lazenyuk-dmitry/SterringWheel/assets/80mm-brushless-fan-sunon-kd1208ptb1-2.snapshot.12/80mm brushless fan (SUNON KD1208PTB1)top.JPG

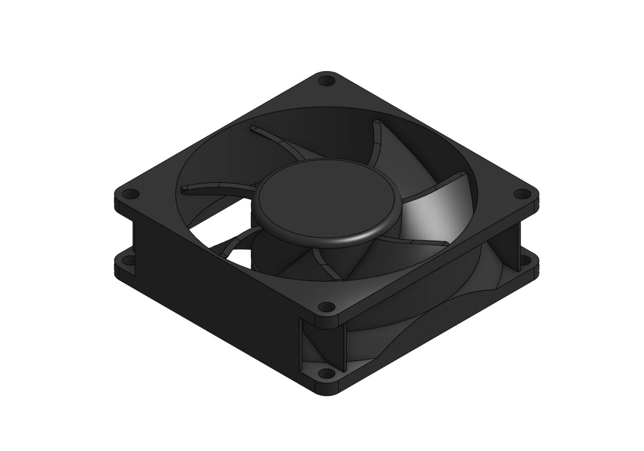
assets/80mm-brushless-fan-sunon-kd1208ptb1-2.snapshot.12/80mm brushless fan (SUNON KD1208PTB1)top.JPG
