lazenyuk-dmitry/SterringWheel/assets/bts7960-43a-high-power-h-bridge-module-1.snapshot.10/BTS7960 43A HIGH POWER H BRIDGE MODULE.JPG

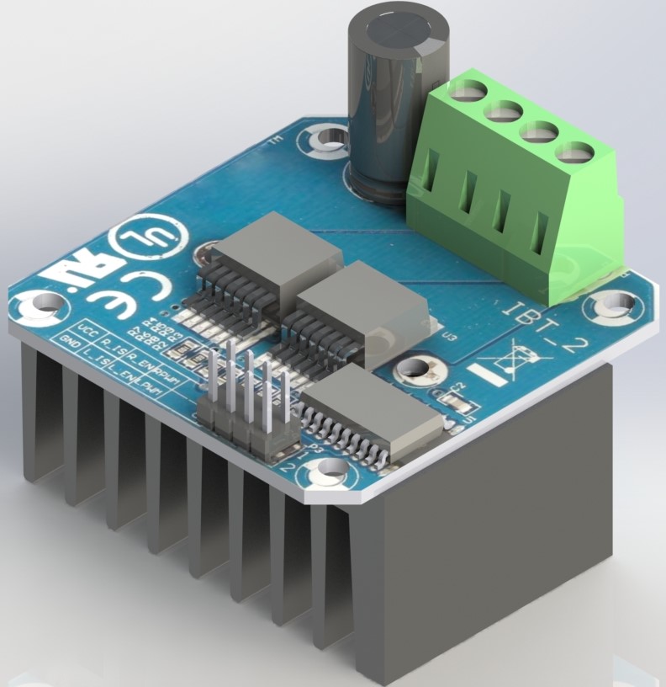
assets/bts7960-43a-high-power-h-bridge-module-1.snapshot.10/BTS7960 43A HIGH POWER H BRIDGE MODULE.JPG
