lazenyuk-dmitry/SterringWheel/assets/connector-5-5x2-5-dc00990-b-1.snapshot.1/Connector_5,5-2,5_DC00990-B_01.png

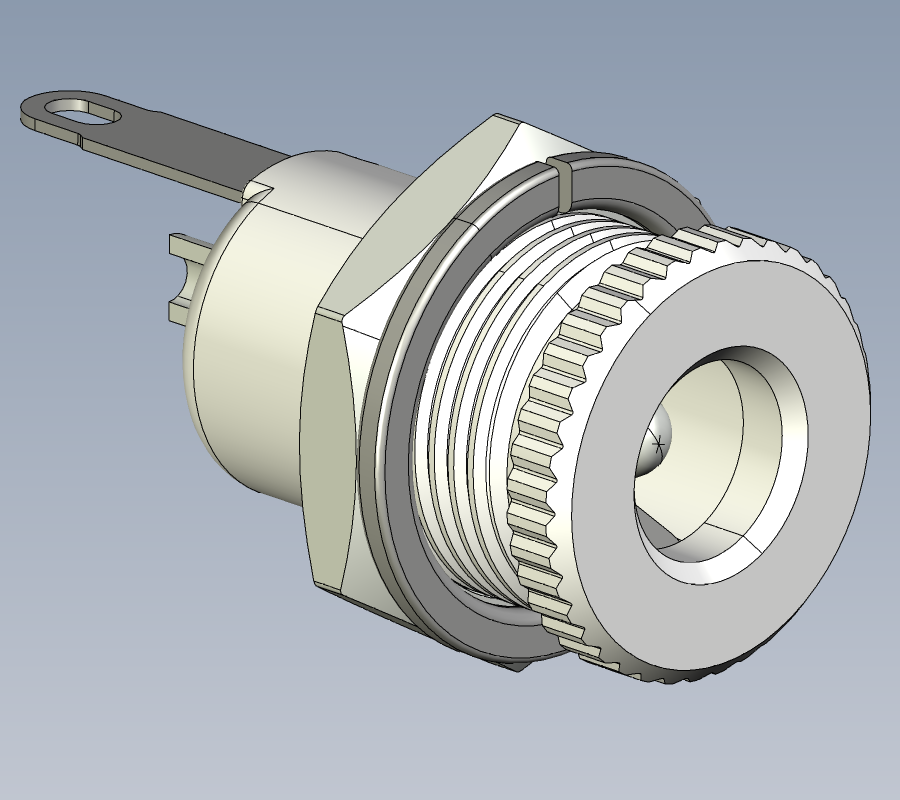
assets/connector-5-5x2-5-dc00990-b-1.snapshot.1/Connector_5,5-2,5_DC00990-B_01.png
