lazenyuk-dmitry/SterringWheel/assets/dc-motor-rs-775-12v-12000-rpm-1.snapshot.1/Capture - 2.PNG

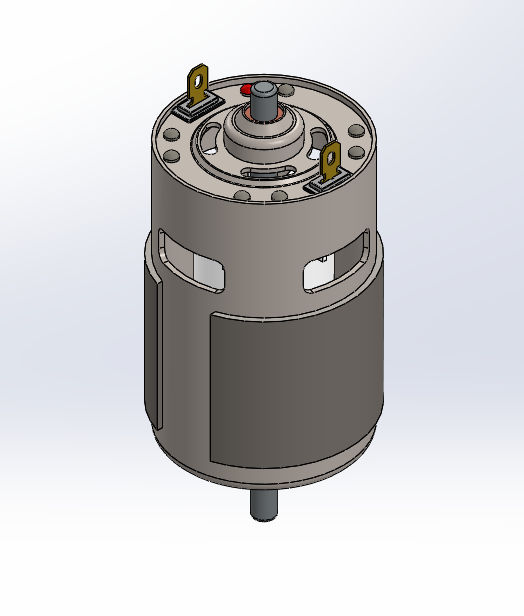
assets/dc-motor-rs-775-12v-12000-rpm-1.snapshot.1/Capture - 2.PNG
