lazenyuk-dmitry/SterringWheel/assets/encoder-36.snapshot.2/untitled.24.jpg

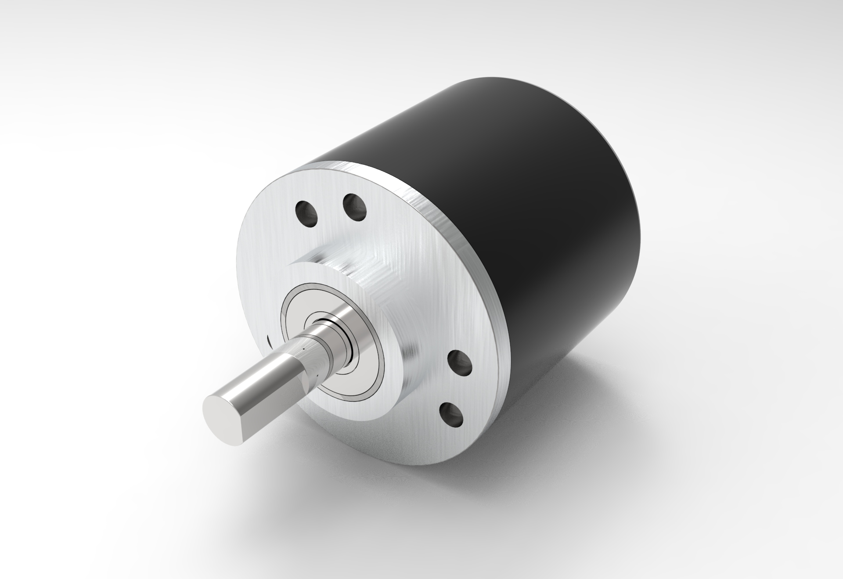
assets/encoder-36.snapshot.2/untitled.24.jpg
