lazenyuk-dmitry/SterringWheel/assets/fanatec-csl-elite-pedals-1.snapshot.8/Rr.png

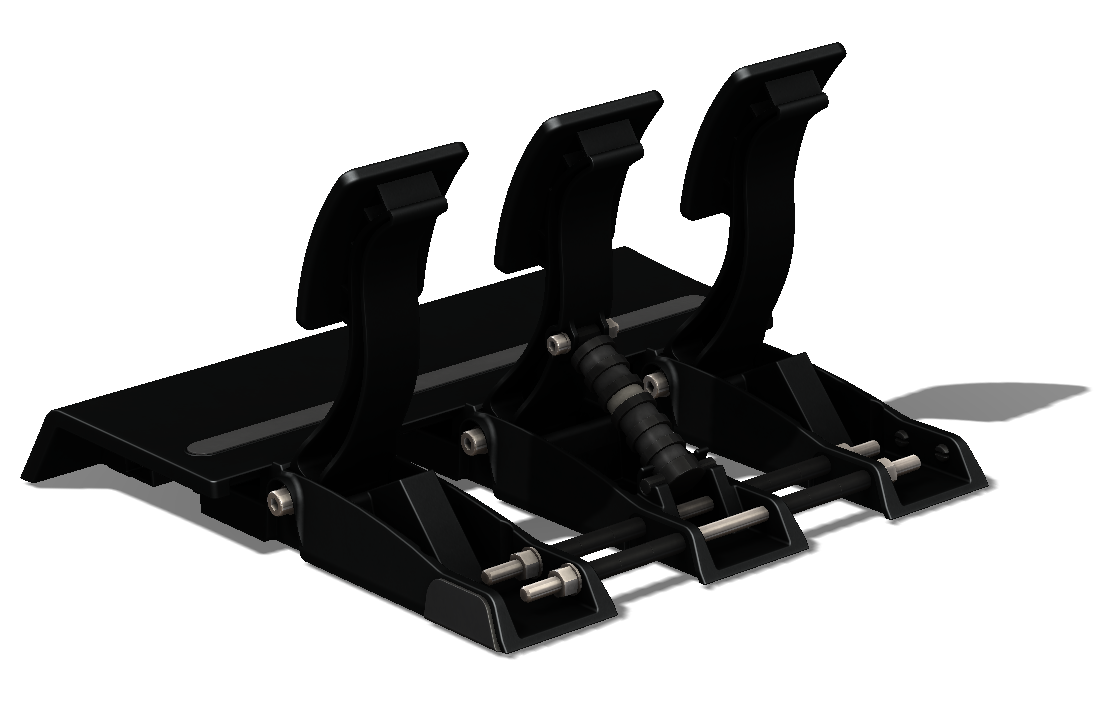
assets/fanatec-csl-elite-pedals-1.snapshot.8/Rr.png
