lazenyuk-dmitry/SterringWheel/assets/fanatec-csp-v2-1.snapshot.5/Renderings/005 gris.png

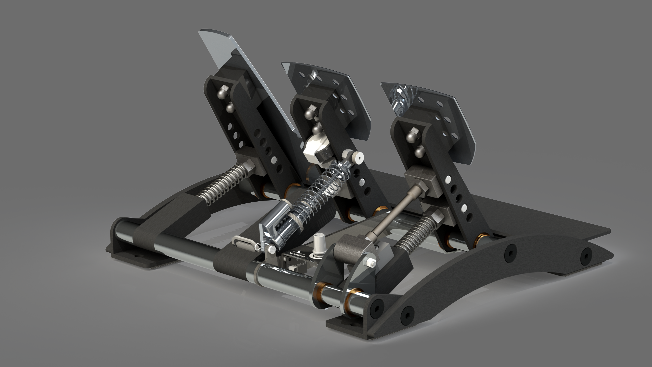
assets/fanatec-csp-v2-1.snapshot.5/Renderings/005 gris.png
