lazenyuk-dmitry/SterringWheel/assets/h-shifter-2.snapshot.1/61ED37vUqIL._SL1019_.jpg

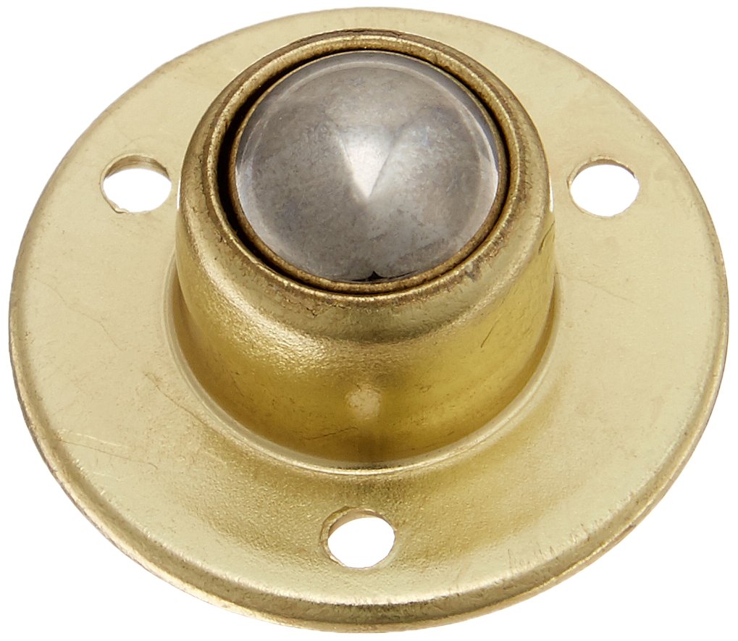
assets/h-shifter-2.snapshot.1/61ED37vUqIL._SL1019_.jpg
