lazenyuk-dmitry/SterringWheel/assets/joy-stick-4.snapshot.1/joy_stick_a2/joy_stick_2a.PNG

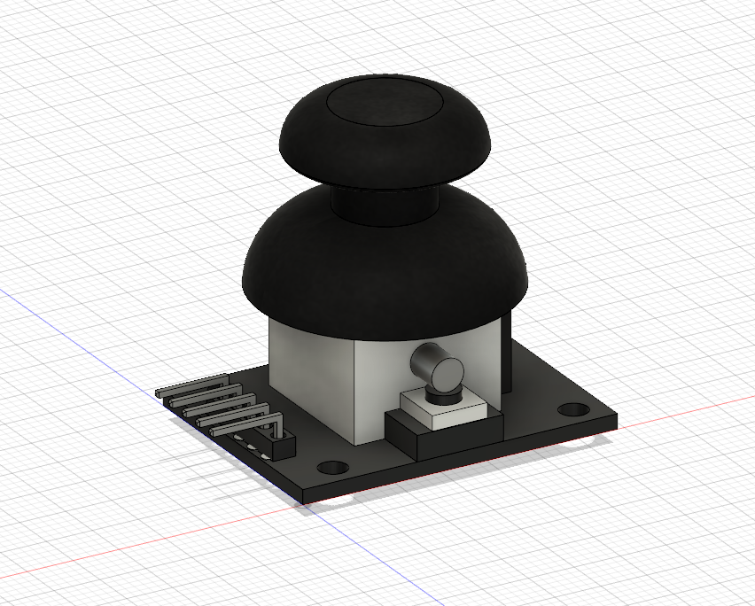
assets/joy-stick-4.snapshot.1/joy_stick_a2/joy_stick_2a.PNG
