lazenyuk-dmitry/SterringWheel/assets/kfl-bearing-or-block-flange-ball-bearing-1.snapshot.10/Bearing KFL series/KFL bearing dimension.JPG

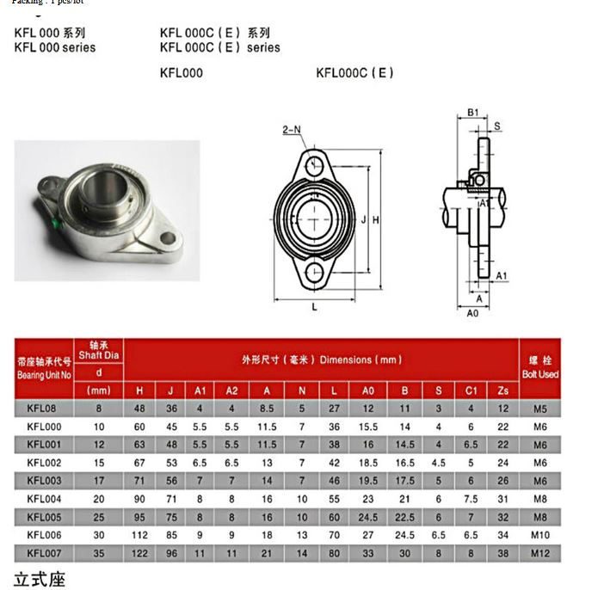
assets/kfl-bearing-or-block-flange-ball-bearing-1.snapshot.10/Bearing KFL series/KFL bearing dimension.JPG
