lazenyuk-dmitry/SterringWheel/assets/kfl-bearing-or-block-flange-ball-bearing-1.snapshot.10/Bearing KFL series/Rendering/KFL006 block flange ball bearing 30 diameter shaft top view.JPG

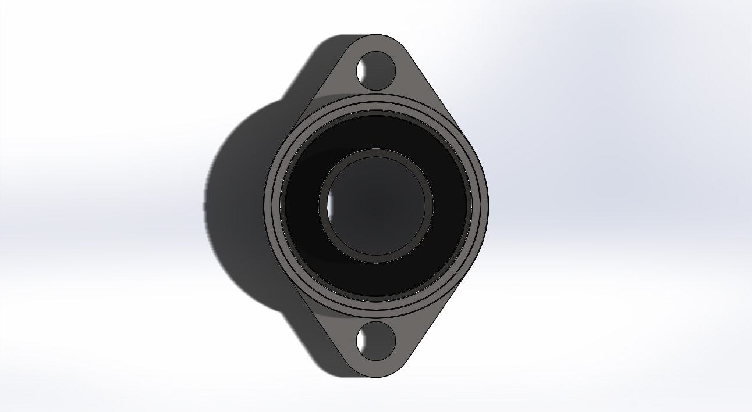
assets/kfl-bearing-or-block-flange-ball-bearing-1.snapshot.10/Bearing KFL series/Rendering/KFL006 block flange ball bearing 30 diameter shaft top view.JPG
