lazenyuk-dmitry/SterringWheel/assets/kfl-bearing-or-block-flange-ball-bearing-1.snapshot.10/Bearing KFL series/Rendering/KFL series with 8 items top.JPG

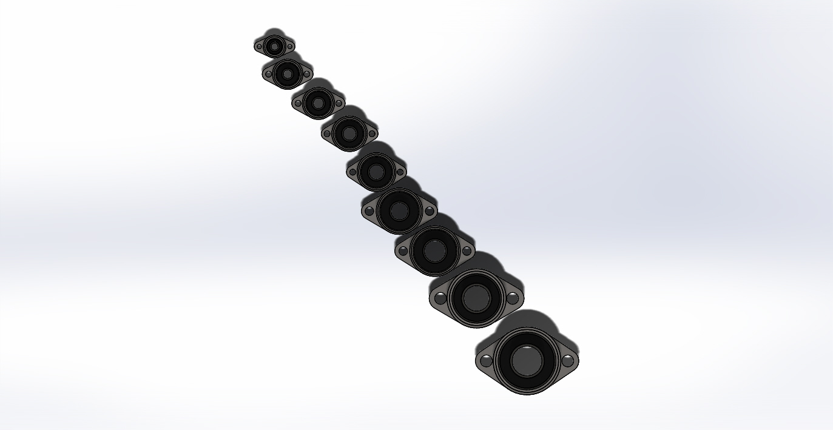
assets/kfl-bearing-or-block-flange-ball-bearing-1.snapshot.10/Bearing KFL series/Rendering/KFL series with 8 items top.JPG
