lazenyuk-dmitry/SterringWheel/assets/lan-rj-45-socket-1.snapshot.3/lan RJ 45 socket.jpg

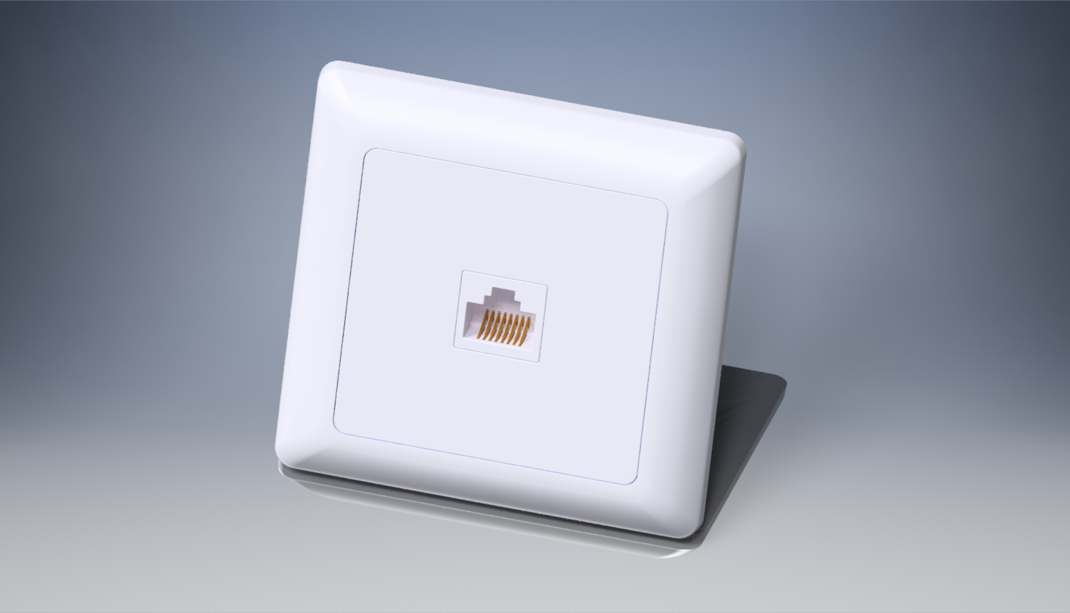
assets/lan-rj-45-socket-1.snapshot.3/lan RJ 45 socket.jpg
