lazenyuk-dmitry/SterringWheel/assets/metal-led-illuminated-latching-16mm-power-push-button-on-off-switch-12v-1.snapshot.2/Metal LED Illuminated Latching 16mm Power Push Button ON-OFF Switch 12V-1.JPG

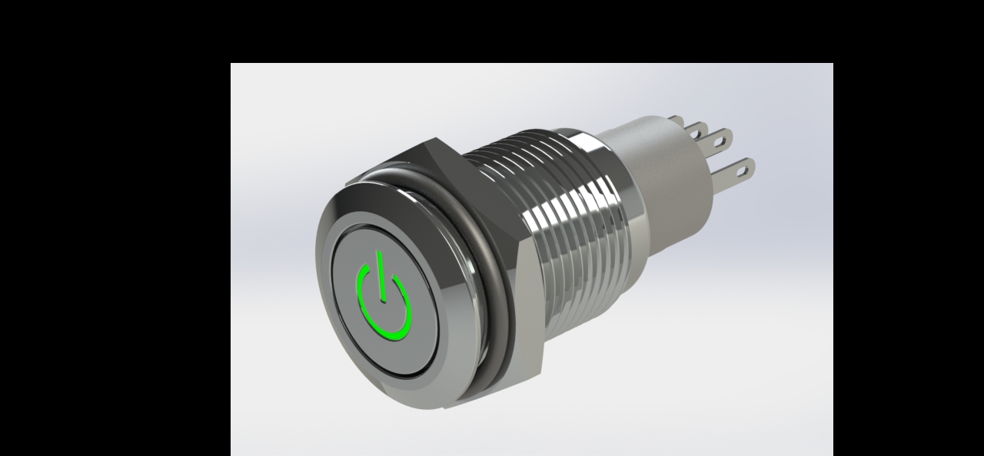
assets/metal-led-illuminated-latching-16mm-power-push-button-on-off-switch-12v-1.snapshot.2/Metal LED Illuminated Latching 16mm Power Push Button ON-OFF Switch 12V-1.JPG
