lazenyuk-dmitry/SterringWheel/assets/micro-switch-with-lever-1.snapshot.3/Micro Switch with Lever.jpg

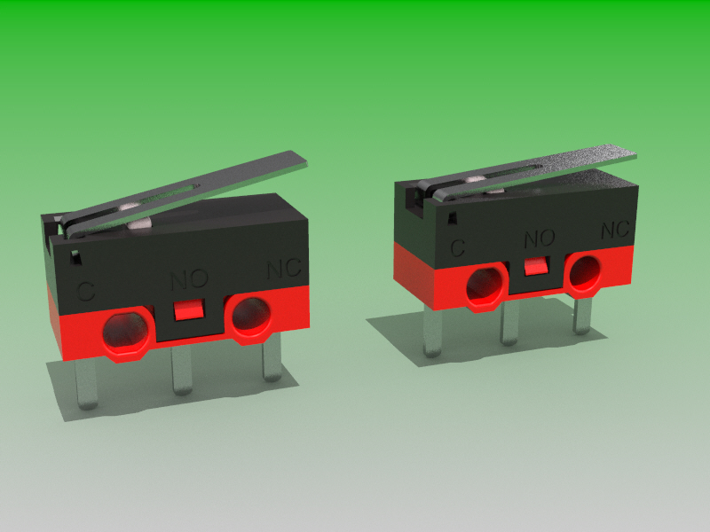
assets/micro-switch-with-lever-1.snapshot.3/Micro Switch with Lever.jpg
