lazenyuk-dmitry/SterringWheel/assets/momentary-push-button-switch-sgi-r13-502-1.snapshot.1/momentary_push_button_sw/momentary_push_button_sw_r13-502p.JPG

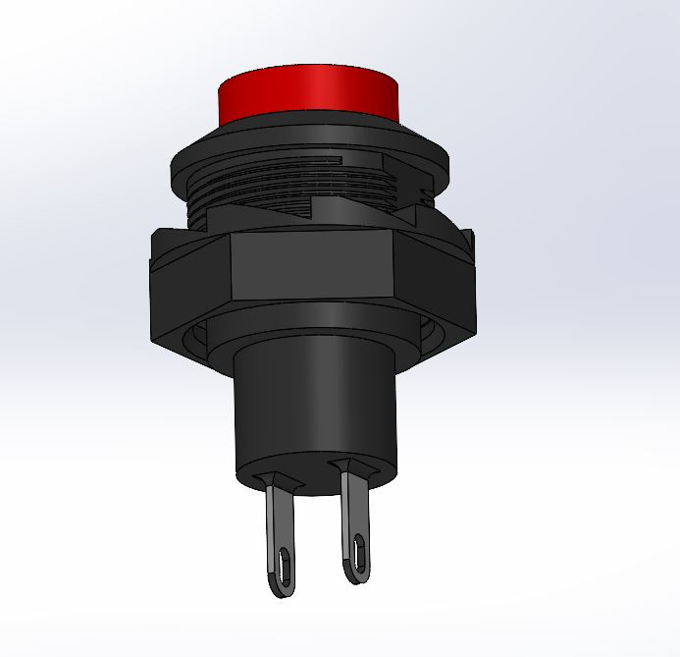
assets/momentary-push-button-switch-sgi-r13-502-1.snapshot.1/momentary_push_button_sw/momentary_push_button_sw_r13-502p.JPG
