lazenyuk-dmitry/SterringWheel/assets/momo-team-300-steering-wheel-1.snapshot.1/momo team 300 steering wheel 2.JPG

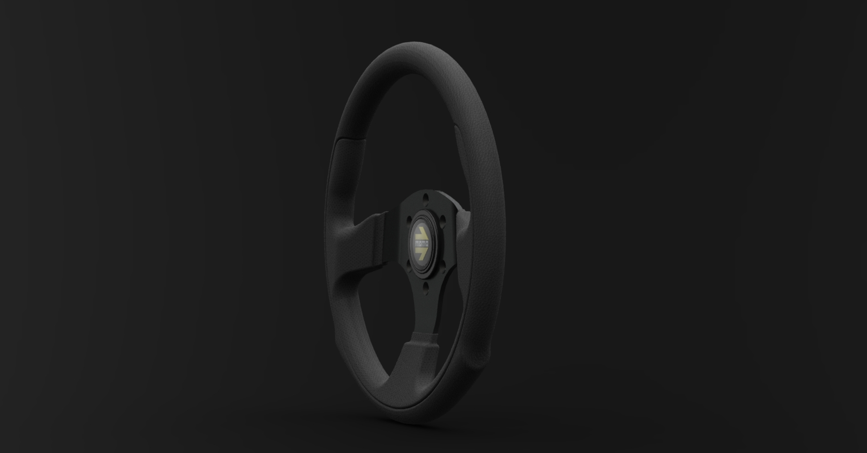
assets/momo-team-300-steering-wheel-1.snapshot.1/momo team 300 steering wheel 2.JPG
