lazenyuk-dmitry/SterringWheel/assets/potentiometer-b10k-3.snapshot.2/potentiometerb10k.jpg

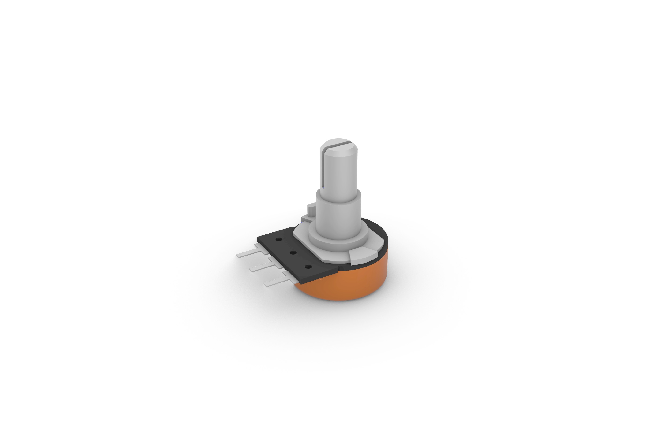
assets/potentiometer-b10k-3.snapshot.2/potentiometerb10k.jpg
