lazenyuk-dmitry/SterringWheel/assets/rocker-switch-arcolectric-r13-112c-aaa-1.snapshot.2/Renderings/Rocker Switch - Arcolectric R13 112C AAA.jpg

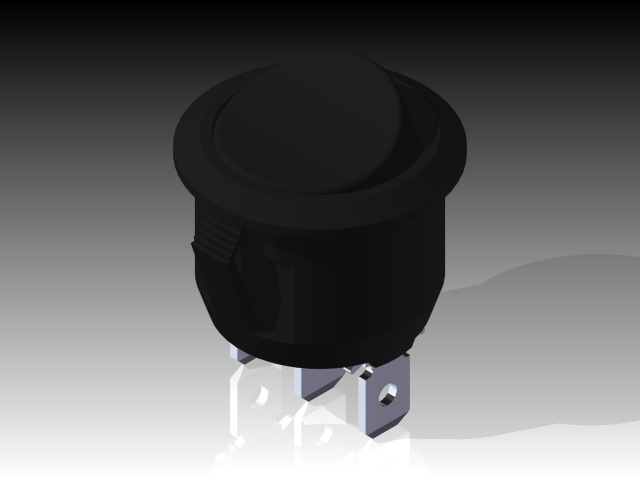
assets/rocker-switch-arcolectric-r13-112c-aaa-1.snapshot.2/Renderings/Rocker Switch - Arcolectric R13 112C AAA.jpg
