lazenyuk-dmitry/SterringWheel/assets/roller-latch/Renderings/pic1.bmp

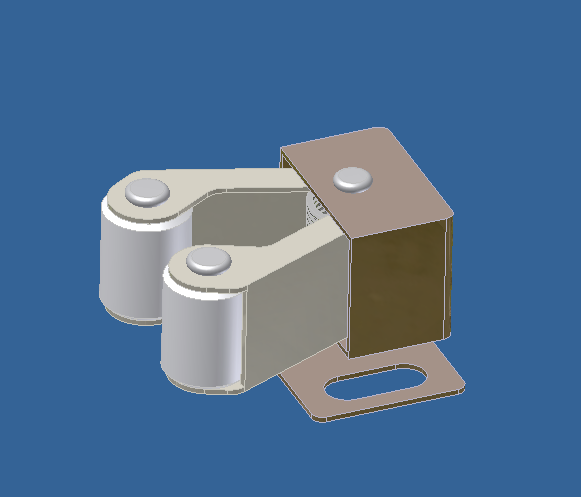
assets/roller-latch/Renderings/pic1.bmp
