lazenyuk-dmitry/SterringWheel/assets/roller-latch/Renderings/pic2.bmp

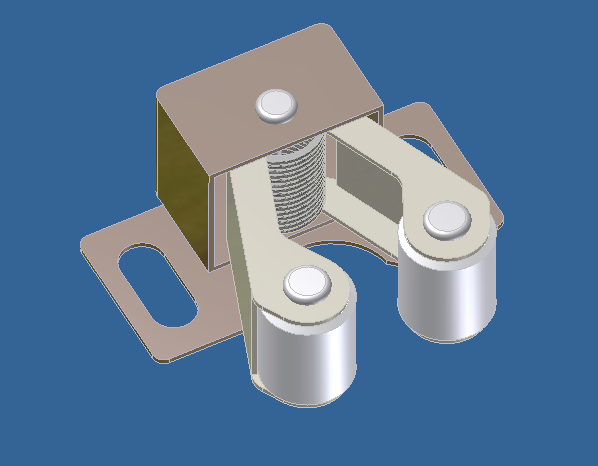
assets/roller-latch/Renderings/pic2.bmp
