lazenyuk-dmitry/SterringWheel/assets/usb-plug-a-1.snapshot.3/USB Plug A.png

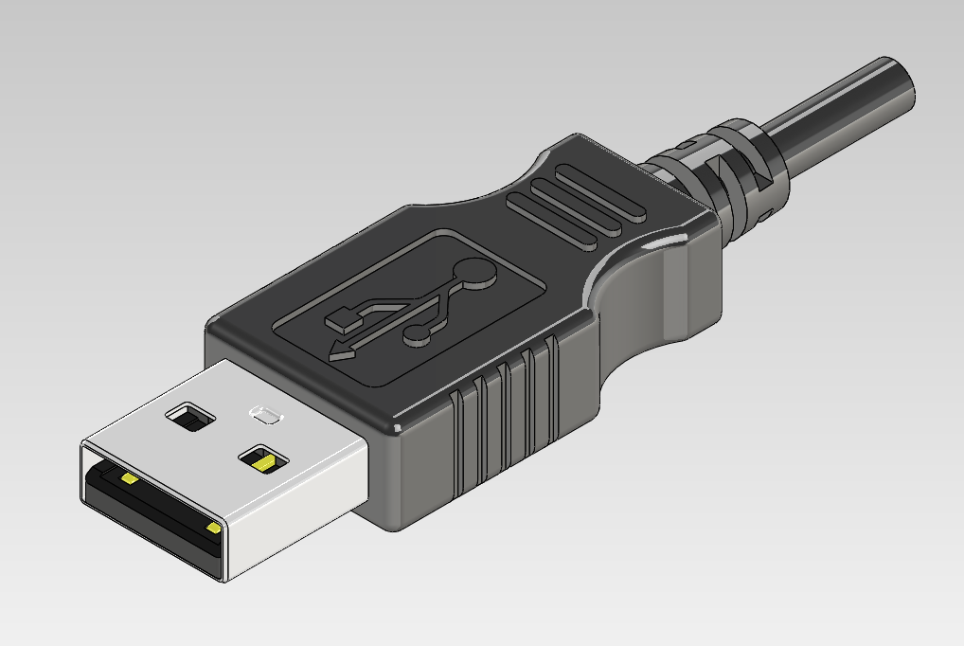
assets/usb-plug-a-1.snapshot.3/USB Plug A.png
