lazenyuk-dmitry/SterringWheel/images/pedals/IMG_20220706_095020.jpg

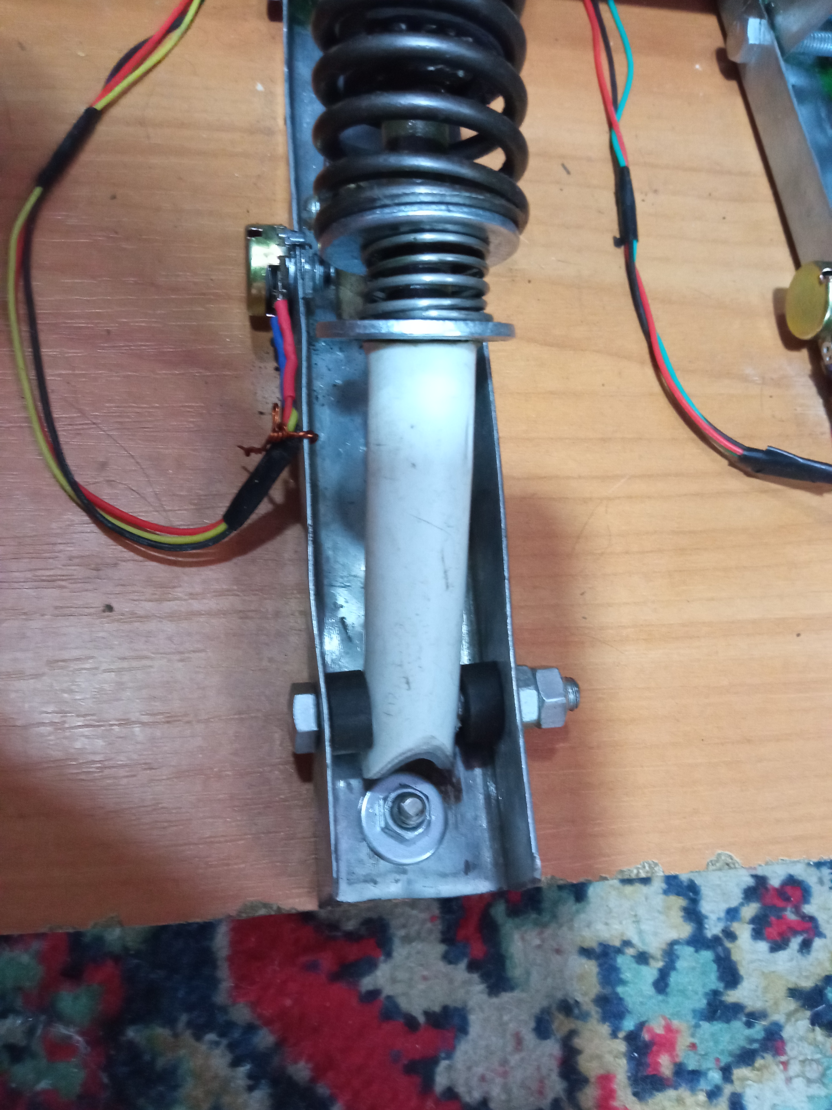
images/pedals/IMG_20220706_095020.jpg
