lazenyuk-dmitry/SterringWheel/images/pedals/IMG_20220706_215036.jpg

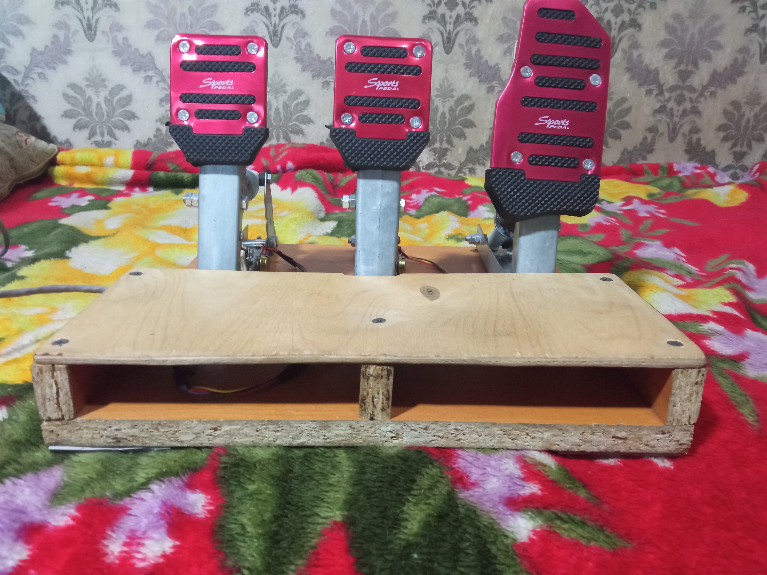
images/pedals/IMG_20220706_215036.jpg
