lazenyuk-dmitry/SterringWheel/images/TopView.png

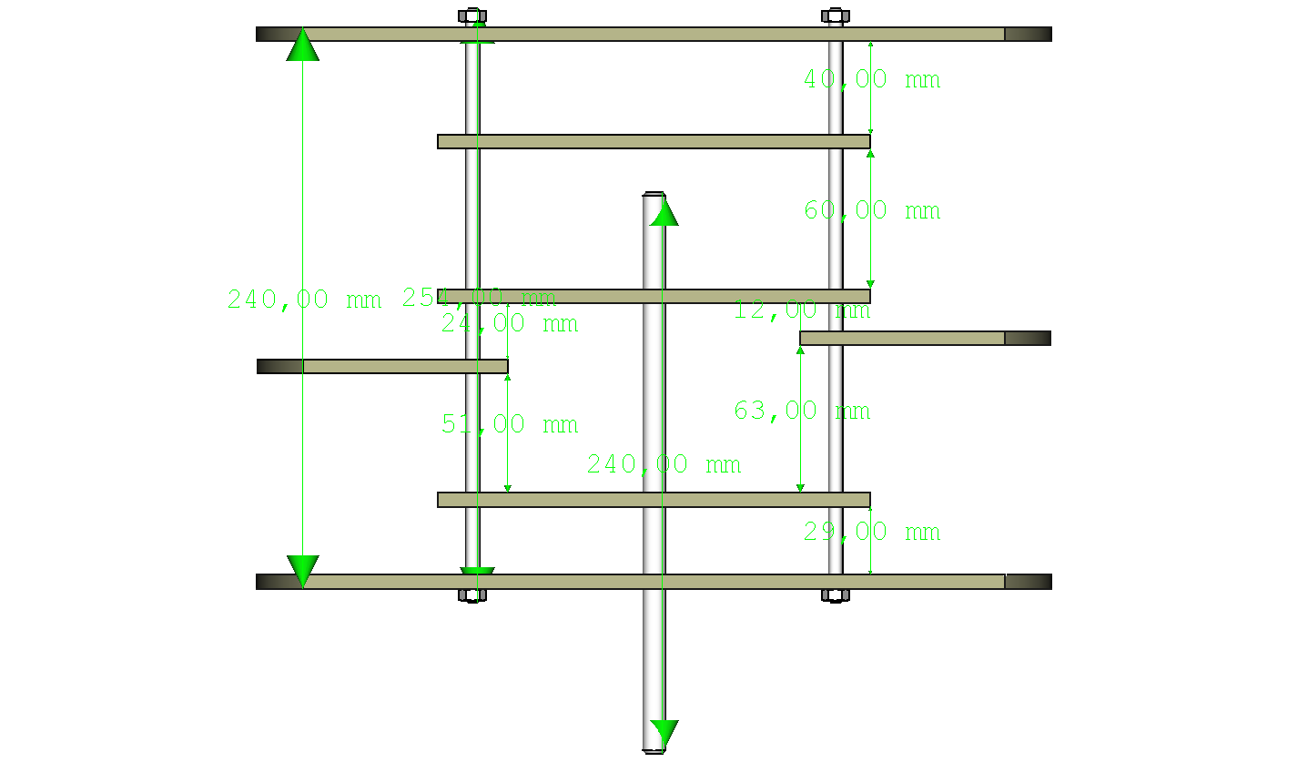
images/TopView.png
