lazenyuk-dmitry/SterringWheel/assets/metal-steering-wheel-1.snapshot.2/vairas.STEP

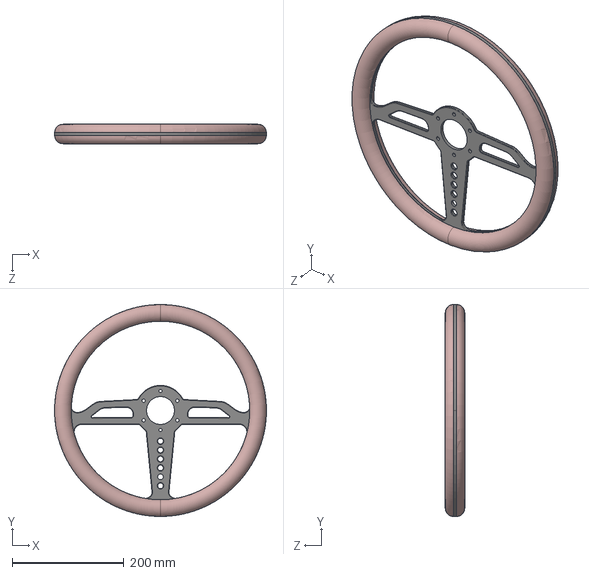
[picture p97: CAD file, 2022-05-22]
assets/metal-steering-wheel-1.snapshot.2/vairas.STEP
380.0 x 380.0 x 35.0 mm
VAIRAS
