lazenyuk-dmitry/SterringWheel/assets/micro-switch-with-lever-1.snapshot.3/Micro Switch with Lever closed.stp

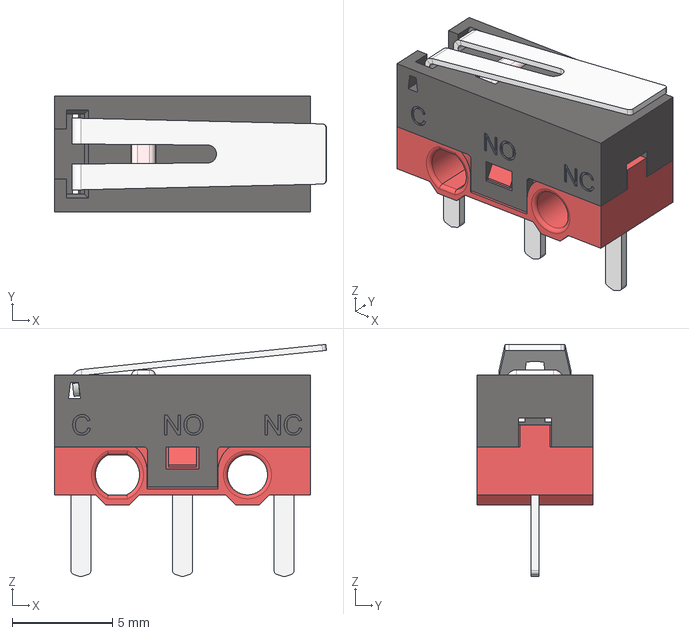
[picture p98: CAD file, 2022-05-21]
assets/micro-switch-with-lever-1.snapshot.3/Micro Switch with Lever closed.stp
13.6 x 5.80 x 11.6 mm
