lazenyuk-dmitry/SterringWheel/assets/momentary-push-button-switch-sgi-r13-502-1.snapshot.1/momentary_push_button_sw/push_button_SGI_R13-502.STEP

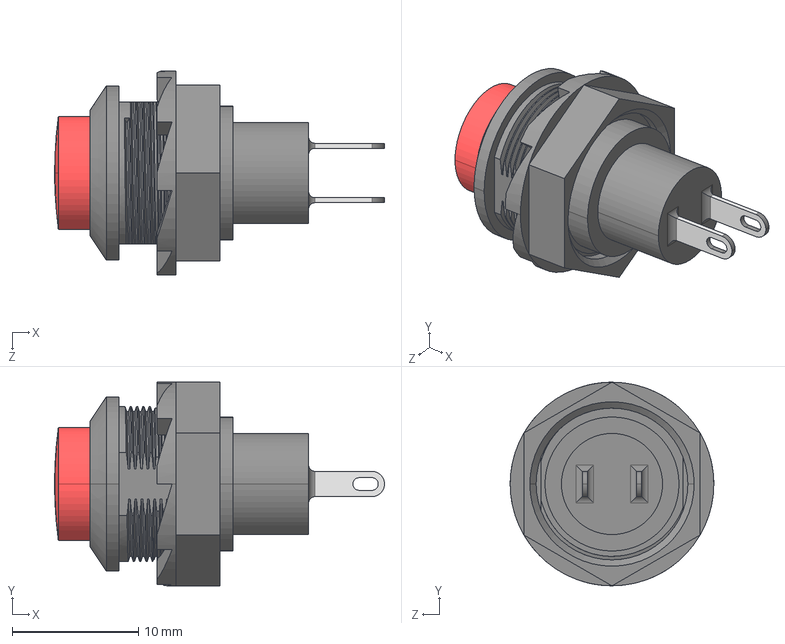
[picture p99: CAD file, 2022-05-15]
assets/momentary-push-button-switch-sgi-r13-502-1.snapshot.1/momentary_push_button_sw/push_button_SGI_R13-502.STEP
26.1 x 16.1 x 16.1 mm
