lazenyuk-dmitry/SterringWheel/assets/nintendo-switch-joystick-1.snapshot.1/Sheet.SLDPRT

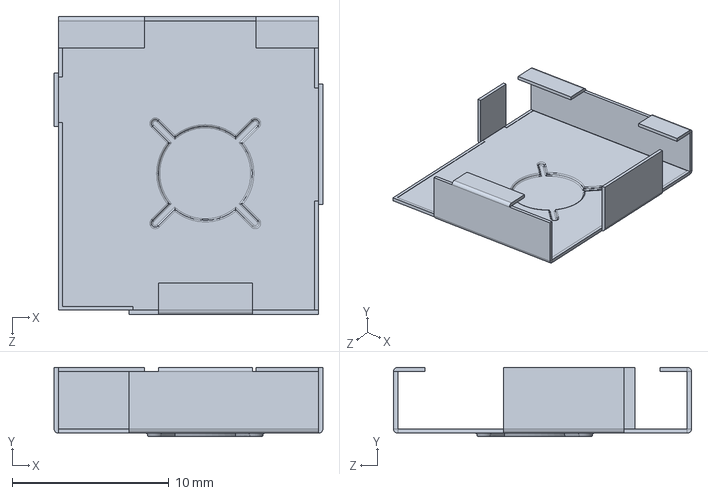
[picture p100: CAD file, 2022-05-16]
assets/nintendo-switch-joystick-1.snapshot.1/Sheet.SLDPRT
17.1 x 4.42 x 19.0 mm
