lazenyuk-dmitry/SterringWheel/assets/potentiometer-b10k-3.snapshot.2/potentiometerb10k.stp

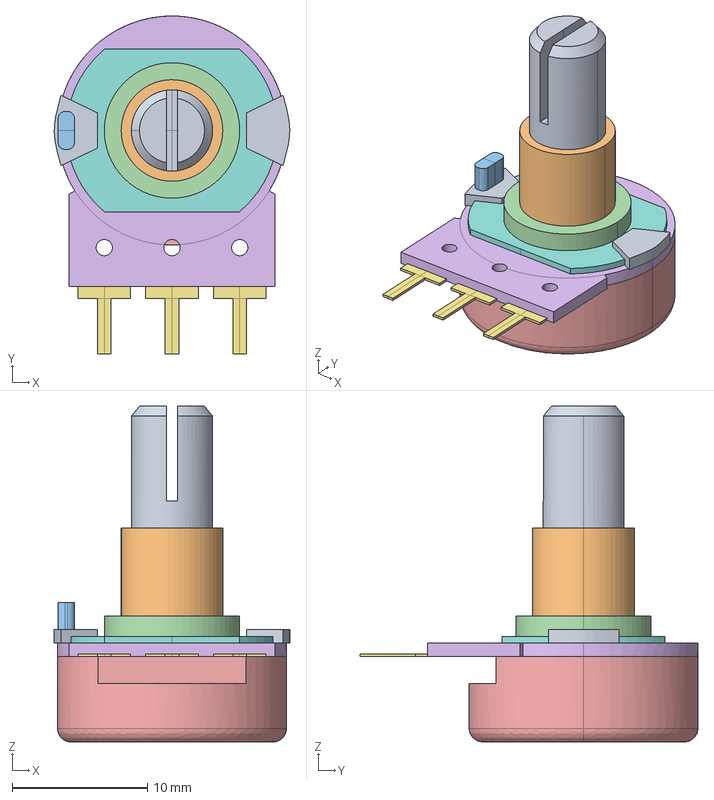
[picture p101: CAD file, 2022-07-06]
assets/potentiometer-b10k-3.snapshot.2/potentiometerb10k.stp
17.4 x 24.9 x 24.8 mm
