lazenyuk-dmitry/SterringWheel/assets/rocker-switch-arcolectric-r13-112c-aaa-1.snapshot.2/Rocker Switch - Arcolectric R13 112C AAA.stp

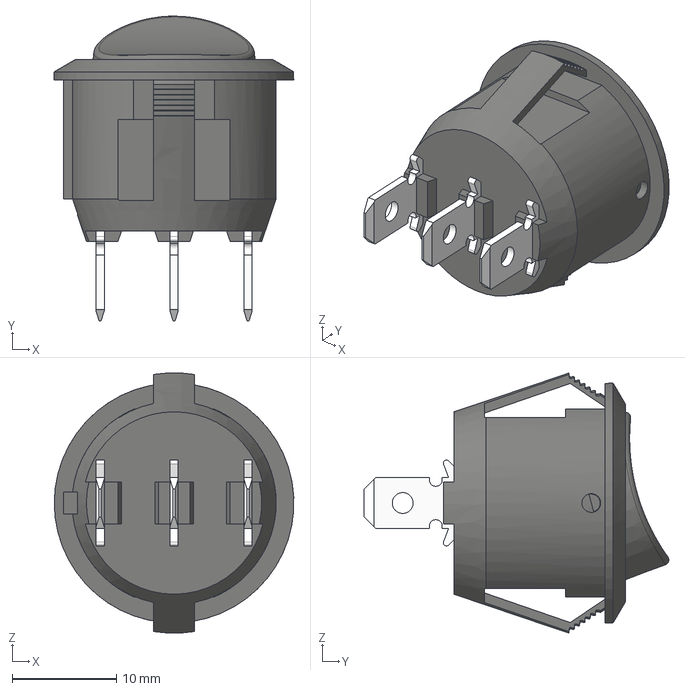
[picture p102: CAD file, 2022-05-13]
assets/rocker-switch-arcolectric-r13-112c-aaa-1.snapshot.2/Rocker Switch - Arcolectric R13 112C AAA.stp
23.0 x 29.2 x 25.0 mm
