lazenyuk-dmitry/SterringWheel/assets/roller-latch/roller latch.stl

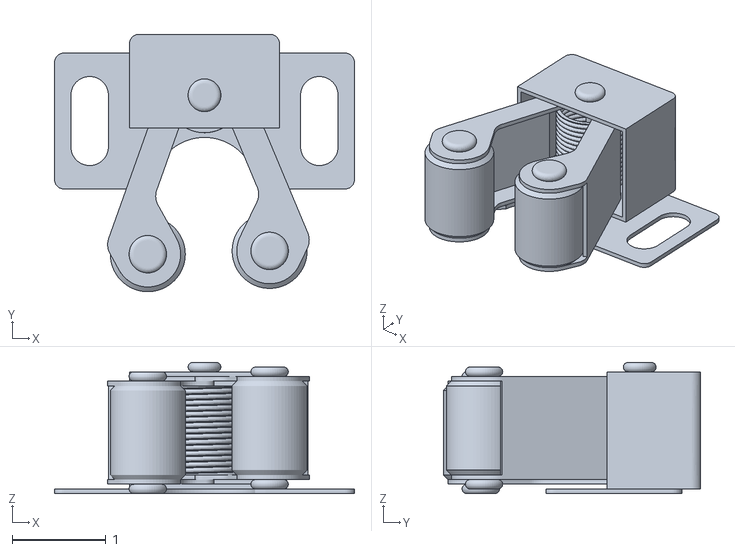
[picture p103: CAD file, 2022-09-12]
assets/roller-latch/roller latch.stl
3.20 x 2.75 x 1.40
