lazenyuk-dmitry/SterringWheel/assets/usb-plug-a-1.snapshot.3/USB Plug A.STEP

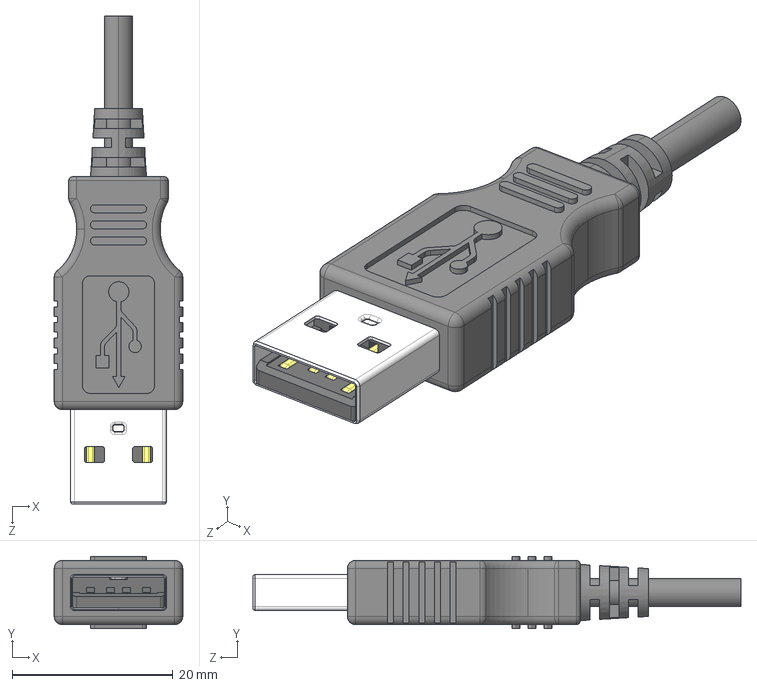
[picture p104: CAD file, 2022-05-13]
assets/usb-plug-a-1.snapshot.3/USB Plug A.STEP
16.0 x 9.00 x 60.8 mm
