lazenyuk-dmitry/SterringWheel/HandBrake.FCStd

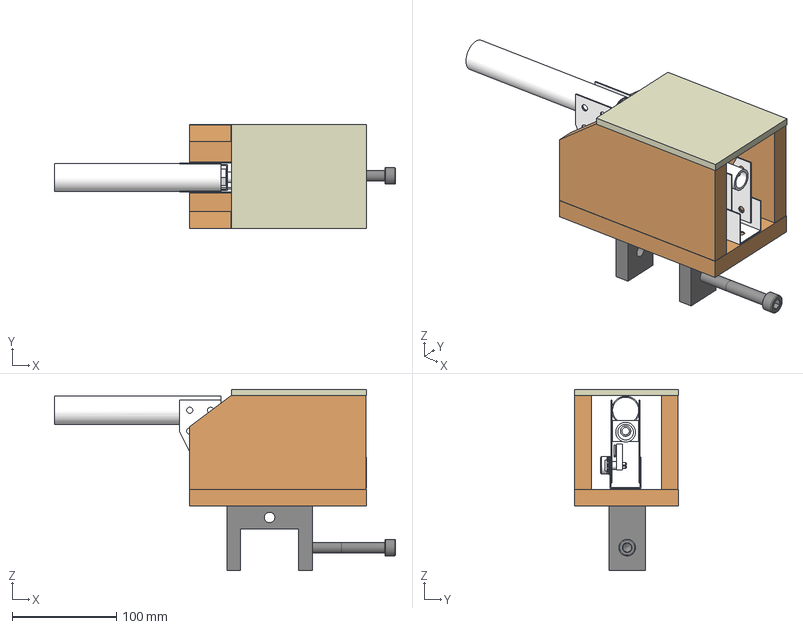
[picture p105: CAD file, 2022-09-12]
HandBrake.FCStd
327.8 x 100.3 x 174.0 mm
Рычаг
Пластина
Крепление пружины
M10x110.0-ThreadedRod
M10-Nut
Пластина (mirrored)
Основание
Пластина001
Втулка упор пружины
Пластина001 (mirrored)
Рычаг потенциометра
Штанга потенциометра
Короб основа
Боковина
Боковина (mirrored)
струбцина
M10x75-Screw
Крышка
