lazenyuk-dmitry/SterringWheel/assets/bts7960-43a-high-power-h-bridge-module-1.snapshot.10/ALUMINUM ELECTROLYTIC CAPACITOR, 330 uF, BTS7960 43A HIGH POWER H BRIDGE MODULE.SLDPRT

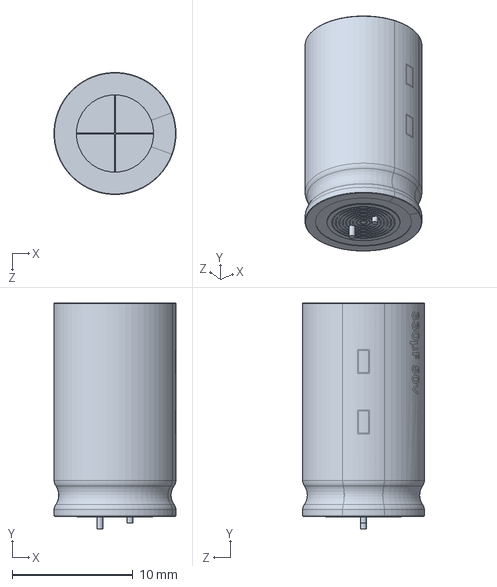
[picture p106: CAD file, 2022-05-12]
assets/bts7960-43a-high-power-h-bridge-module-1.snapshot.10/ALUMINUM ELECTROLYTIC CAPACITOR, 330 uF, BTS7960 43A HIGH POWER H BRIDGE MODULE.SLDPRT
10.1 x 18.7 x 10.1 mm
