lazenyuk-dmitry/SterringWheel/assets/fanatec-csp-v2-1.snapshot.5/05 - Equerre fixation sol 2.SLDPRT

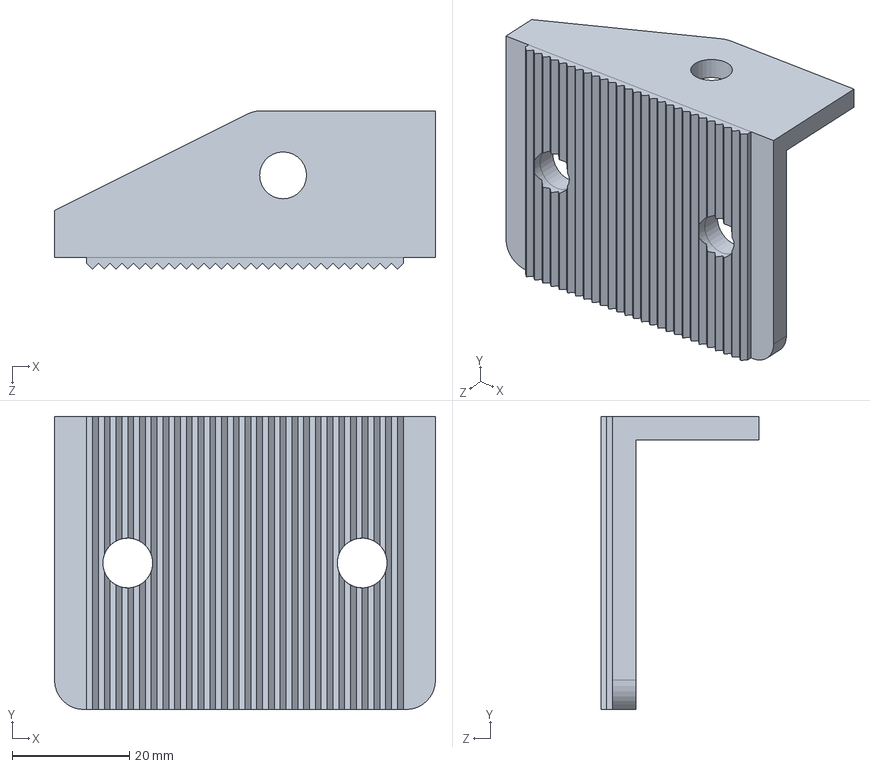
[picture p107: CAD file, 2022-07-06]
assets/fanatec-csp-v2-1.snapshot.5/05 - Equerre fixation sol 2.SLDPRT
65.0 x 50.0 x 27.0 mm
