lazenyuk-dmitry/SterringWheel/assets/kfl-bearing-or-block-flange-ball-bearing-1.snapshot.10/Bearing KFL series/KFL005 block flange ball bearing 25 diameter shaft.SLDPRT

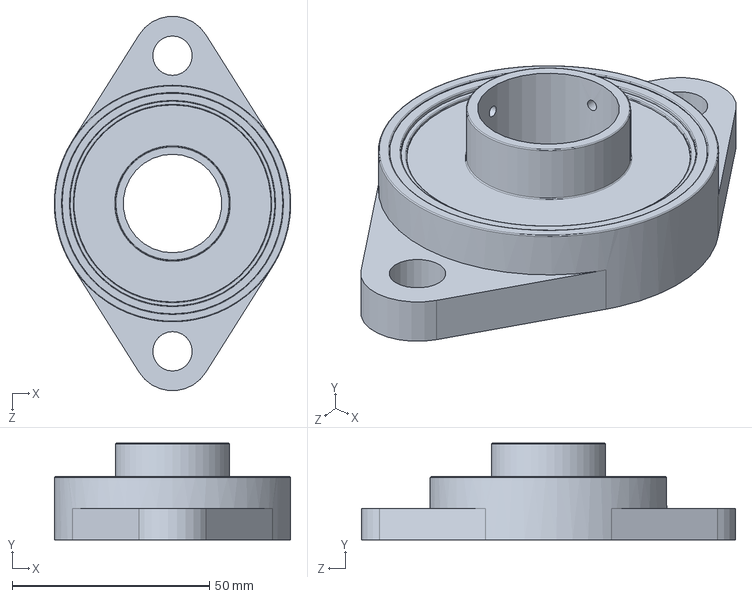
[picture p108: CAD file, 2022-05-09]
assets/kfl-bearing-or-block-flange-ball-bearing-1.snapshot.10/Bearing KFL series/KFL005 block flange ball bearing 25 diameter shaft.SLDPRT
60.0 x 24.5 x 94.9 mm
