lazenyuk-dmitry/SterringWheel/assets/kfl-bearing-or-block-flange-ball-bearing-1.snapshot.10/step files/KFL003 block flange ball bearing 17 diameter shaft.STEP

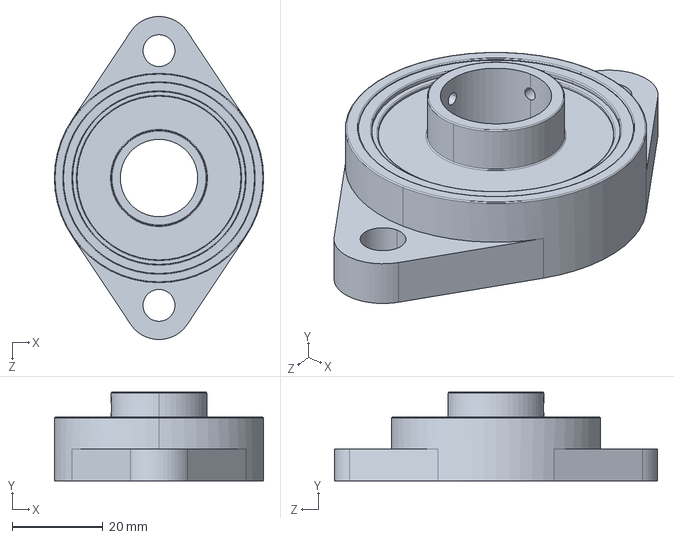
[picture p109: CAD file, 2022-05-09]
assets/kfl-bearing-or-block-flange-ball-bearing-1.snapshot.10/step files/KFL003 block flange ball bearing 17 diameter shaft.STEP
46.0 x 19.5 x 71.0 mm
