lazenyuk-dmitry/SterringWheel/assets/metal-steering-wheel-1.snapshot.2/Metalinis vairas.STEP

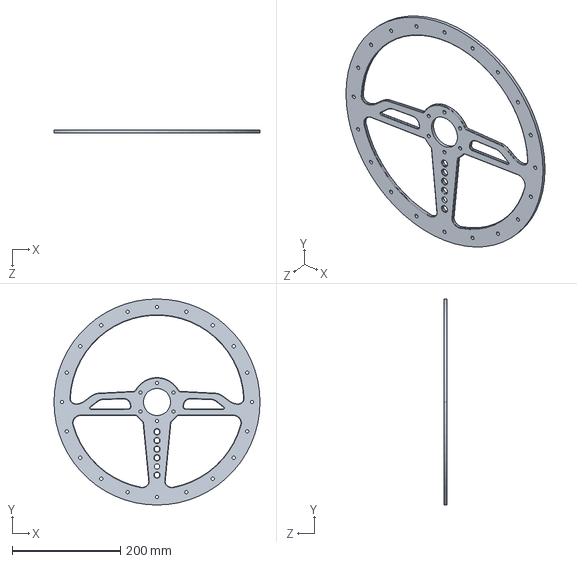
[picture p110: CAD file, 2022-05-22]
assets/metal-steering-wheel-1.snapshot.2/Metalinis vairas.STEP
380.0 x 380.0 x 5.00 mm
