lazenyuk-dmitry/SterringWheel/assets/micro-switch-with-lever-1.snapshot.3/Micro Switch with Lever open.stp

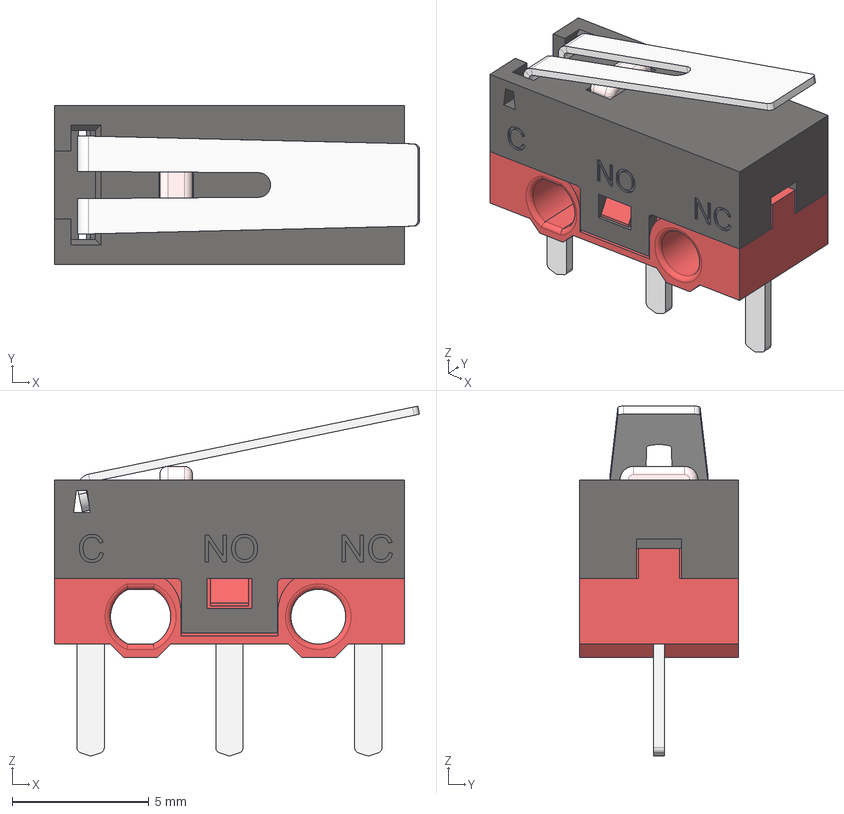
[picture p111: CAD file, 2022-05-21]
assets/micro-switch-with-lever-1.snapshot.3/Micro Switch with Lever open.stp
13.4 x 5.80 x 12.8 mm
