lazenyuk-dmitry/SterringWheel/assets/nintendo-switch-joystick-1.snapshot.1/Switch Joystick.STEP

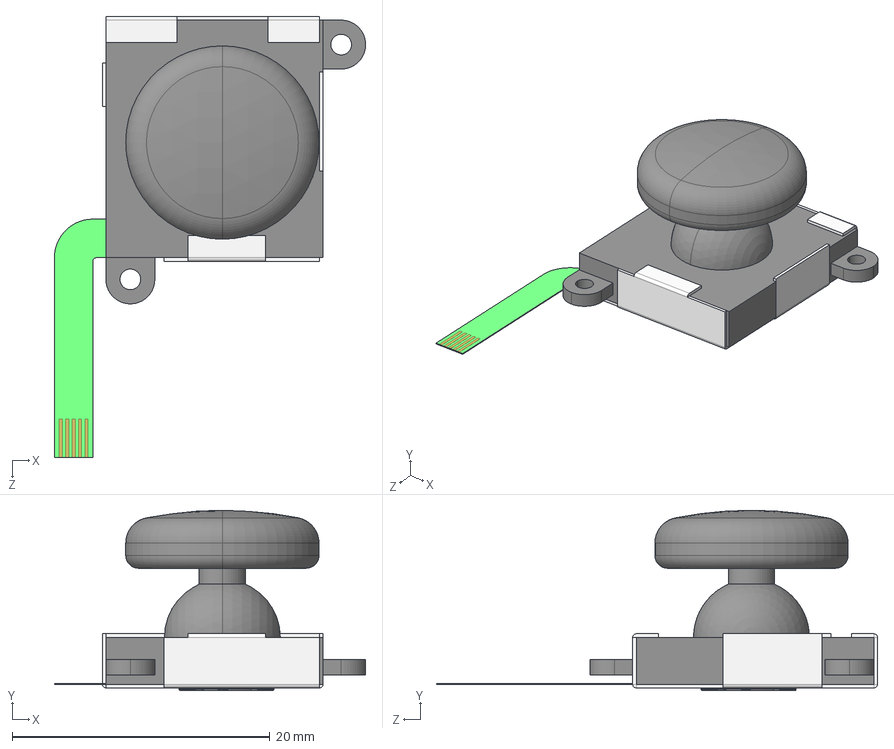
[picture p112: CAD file, 2022-05-16]
assets/nintendo-switch-joystick-1.snapshot.1/Switch Joystick.STEP
24.2 x 14.0 x 34.2 mm
Sheet
Part3^Switch Joystick
