lazenyuk-dmitry/SterringWheel/Pedals.FCStd

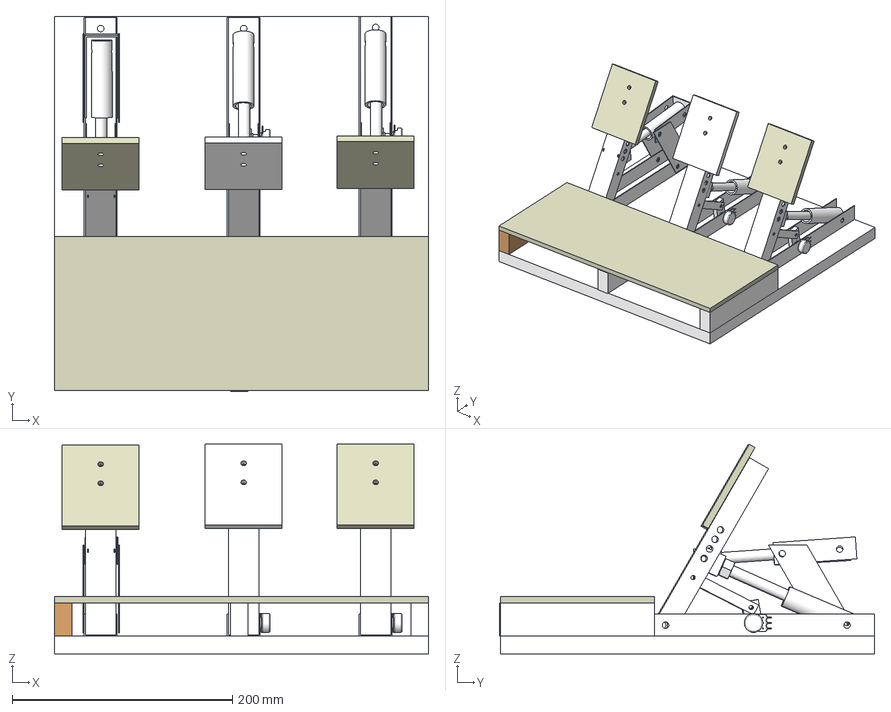
[picture p113: CAD file, 2022-07-19]
Pedals.FCStd
340.0 x 341.0 x 190.5 mm
Рычаг педали
Основа педали
Втулка упор пружины
Крепление пружины
M10x110.0-ThreadedRod
M10-Nut
M10-Nut001
Рычаг потенциометра
Штанга потенциометра
Накладка
Основа педали001
Рычаг
Крепление пружины001
Втулка
M10x95.0-ThreadedRod
Накладка001
Опора втулки
Опора втулки001
Качелька
Педаль Тормоз
Основание
Боковина
Боковина001
Крышка
Центральная подпорка
