lazenyuk-dmitry/SterringWheel/assets/bts7960-43a-high-power-h-bridge-module-1.snapshot.10/8 PIN HEADER, IC, BTS7960 43A HIGH POWER H BRIDGE MODULE.SLDPRT

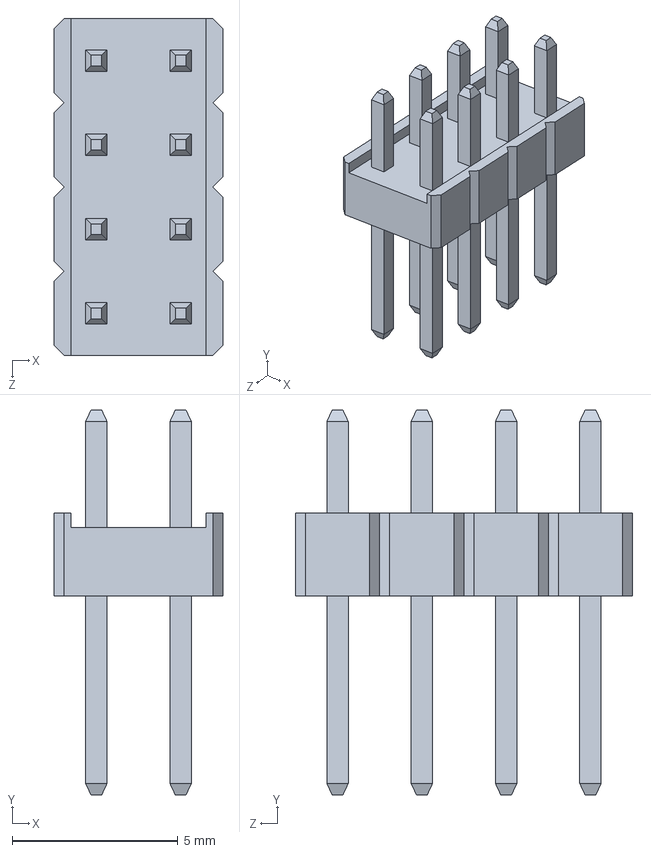
[picture p114: CAD file, 2022-05-12]
assets/bts7960-43a-high-power-h-bridge-module-1.snapshot.10/8 PIN HEADER, IC, BTS7960 43A HIGH POWER H BRIDGE MODULE.SLDPRT
5.08 x 11.6 x 10.2 mm
