lazenyuk-dmitry/SterringWheel/assets/fanatec-csp-v2-1.snapshot.5/18 - Vibreur.SLDPRT

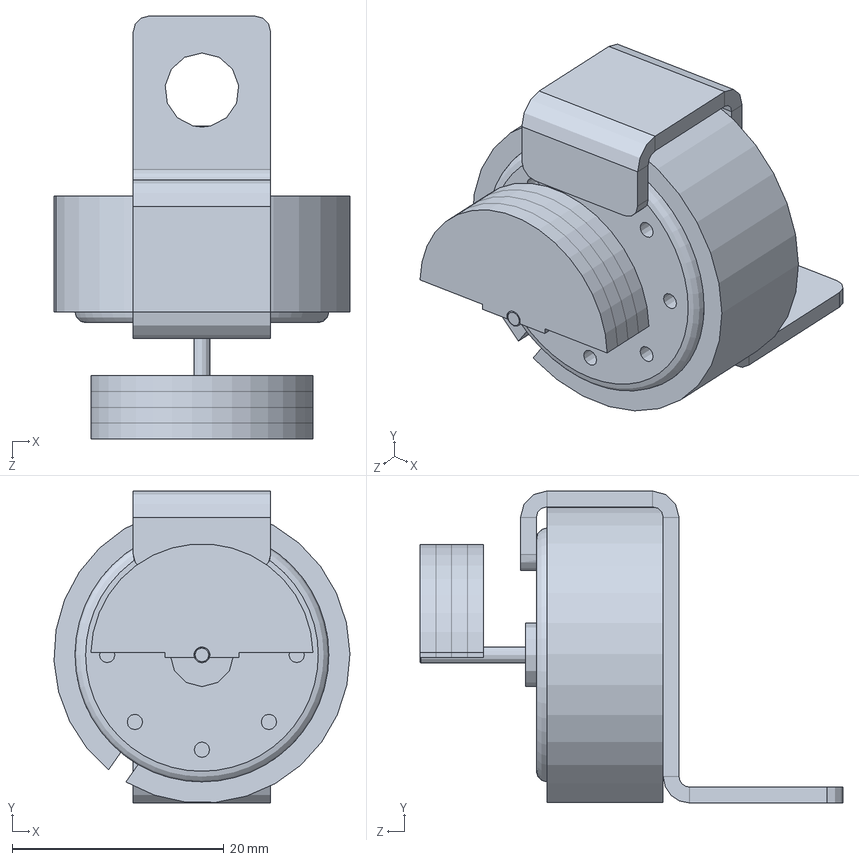
[picture p115: CAD file, 2022-07-06]
assets/fanatec-csp-v2-1.snapshot.5/18 - Vibreur.SLDPRT
28.0 x 29.5 x 40.0 mm
