lazenyuk-dmitry/SterringWheel/assets/kfl-bearing-or-block-flange-ball-bearing-1.snapshot.10/step files/KFL006 block flange ball bearing 30 diameter shaft.STEP

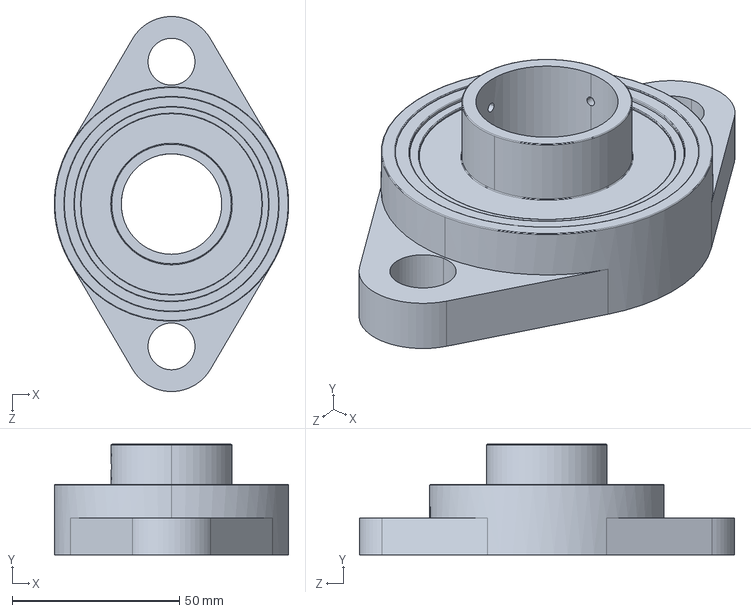
[picture p116: CAD file, 2022-05-09]
assets/kfl-bearing-or-block-flange-ball-bearing-1.snapshot.10/step files/KFL006 block flange ball bearing 30 diameter shaft.STEP
70.0 x 33.0 x 112.0 mm
