lazenyuk-dmitry/SterringWheel/PaddleShifter.FCStd

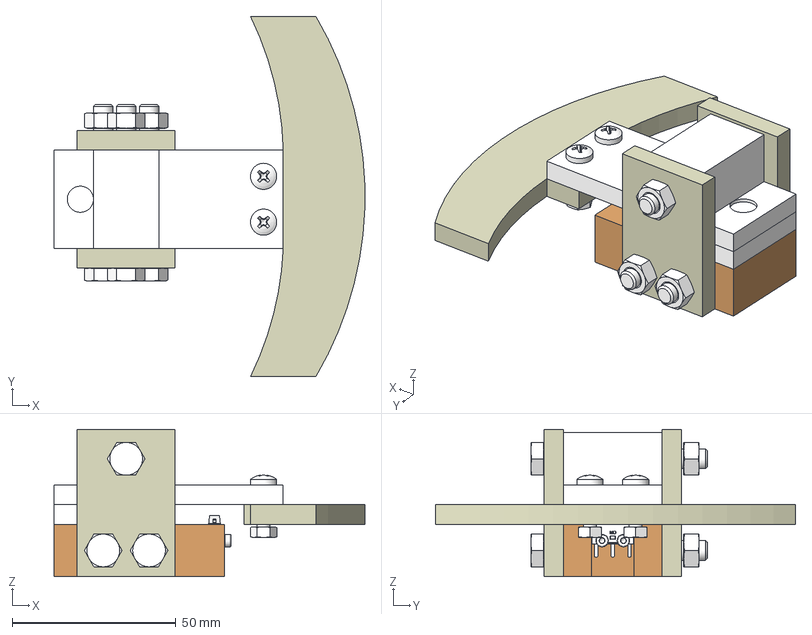
[picture p117: CAD file, 2022-07-06]
PaddleShifter.FCStd
94.9 x 110.0 x 45.0 mm
Основа
Крепление
Switch
Рычаг
Крепление рычага
Неодимовый магнит (8х5)
Лепесток
M4x16-Screw
M4-Nut
M4x16-Screw001
M4-Nut001
Неодимовый магнит (8х5)001
Проставка
M6x50-Screw
M6x50-Screw077
M6x50-Screw078
M6-Nut
M6-Nut085
M6-Nut086
M2x10-Screw
M2x10-Screw001
Крепление001
