lazenyuk-dmitry/SterringWheel/assets/bts7960-43a-high-power-h-bridge-module-1.snapshot.10/EUROSTYLE TERMINAL BLOCK 2 POS 5.0 MM RA PLUG, BTS7960 43A HIGH POWER H BRIDGE MODULE.SLDPRT

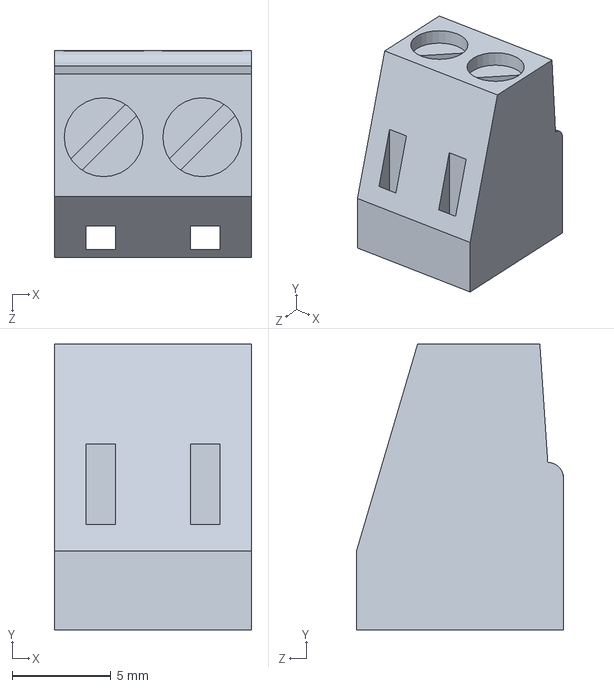
[picture p118: CAD file, 2022-05-12]
assets/bts7960-43a-high-power-h-bridge-module-1.snapshot.10/EUROSTYLE TERMINAL BLOCK 2 POS 5.0 MM RA PLUG, BTS7960 43A HIGH POWER H BRIDGE MODULE.SLDPRT
10.0 x 14.5 x 10.5 mm
