lazenyuk-dmitry/SterringWheel/assets/fanatec-csp-v2-1.snapshot.5/11 - Palier bronze.SLDPRT

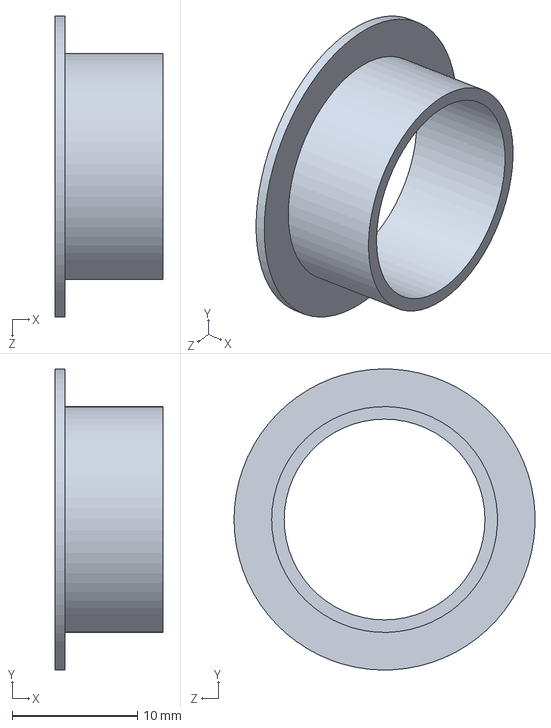
[picture p119: CAD file, 2022-07-06]
assets/fanatec-csp-v2-1.snapshot.5/11 - Palier bronze.SLDPRT
8.60 x 24.0 x 24.0 mm
