lazenyuk-dmitry/SterringWheel/assets/kfl-bearing-or-block-flange-ball-bearing-1.snapshot.10/Bearing KFL series/KFL08 block flange ball bearing 08 diameter shaft.SLDPRT

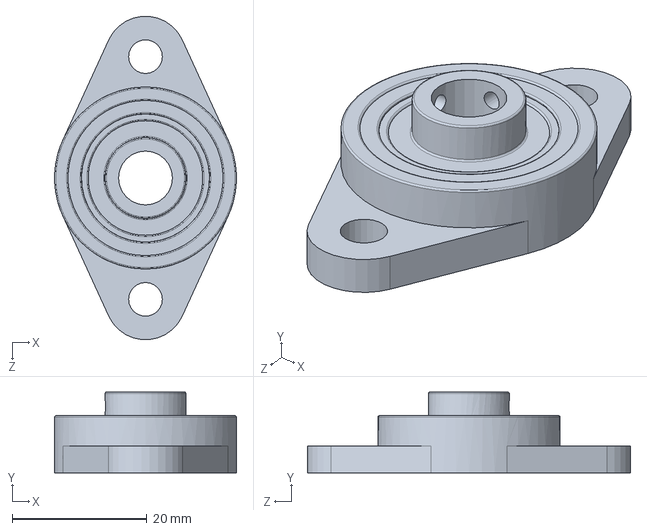
[picture p120: CAD file, 2022-05-09]
assets/kfl-bearing-or-block-flange-ball-bearing-1.snapshot.10/Bearing KFL series/KFL08 block flange ball bearing 08 diameter shaft.SLDPRT
27.0 x 12.0 x 47.9 mm
