lazenyuk-dmitry/SterringWheel/PaddleShifter-v2.FCStd

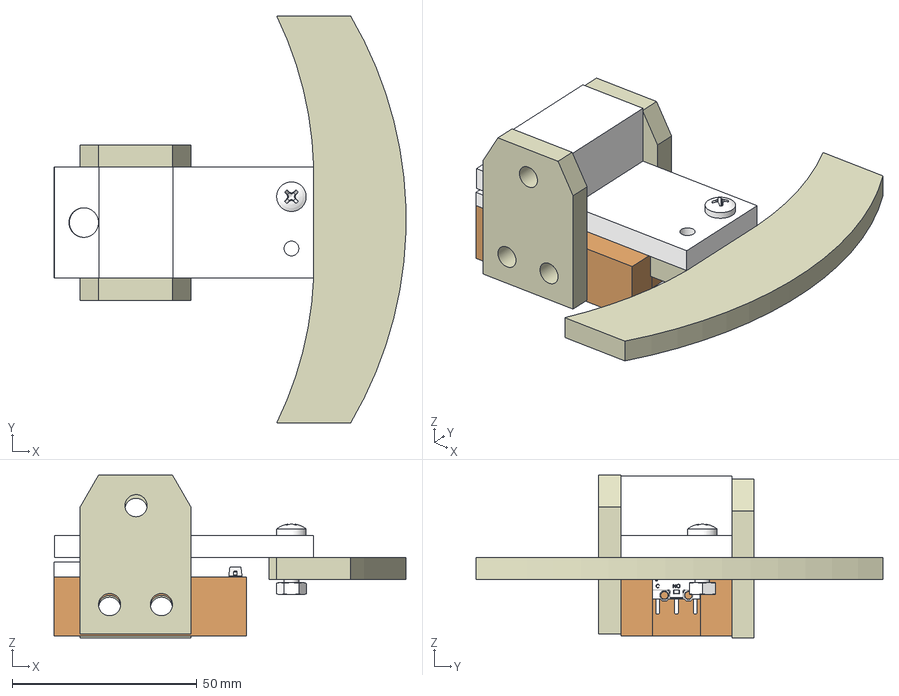
[picture p121: CAD file, 2022-07-06]
PaddleShifter-v2.FCStd
95.1 x 110.0 x 44.0 mm
Основа
Крепление
Switch
Рычаг
Крепление рычага
Неодимовый магнит (8х5)
Лепесток
M4x16-Screw
M4-Nut
Неодимовый магнит (8х5)001
Проставка
Крепление001
