lazenyuk-dmitry/SterringWheel/assets/bts7960-43a-high-power-h-bridge-module-1.snapshot.10/PCB, BTS7960 43A HIGH POWER H BRIDGE MODULE.SLDPRT

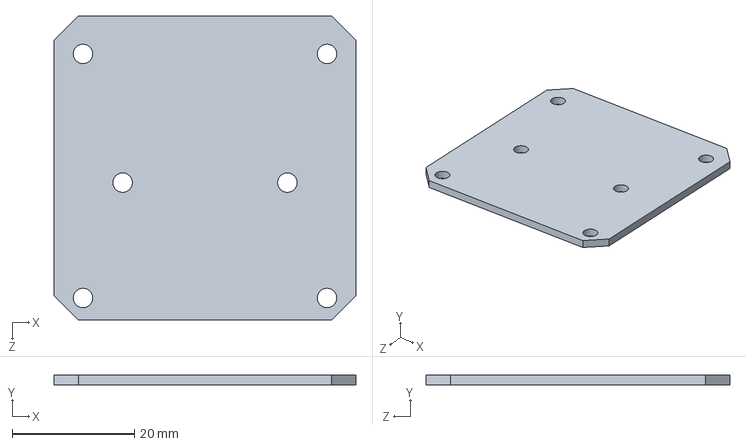
[picture p122: CAD file, 2022-05-12]
assets/bts7960-43a-high-power-h-bridge-module-1.snapshot.10/PCB, BTS7960 43A HIGH POWER H BRIDGE MODULE.SLDPRT
49.5 x 1.70 x 49.8 mm
