lazenyuk-dmitry/SterringWheel/assets/fanatec-csp-v2-1.snapshot.5/47 - Entretoise capteur.SLDPRT

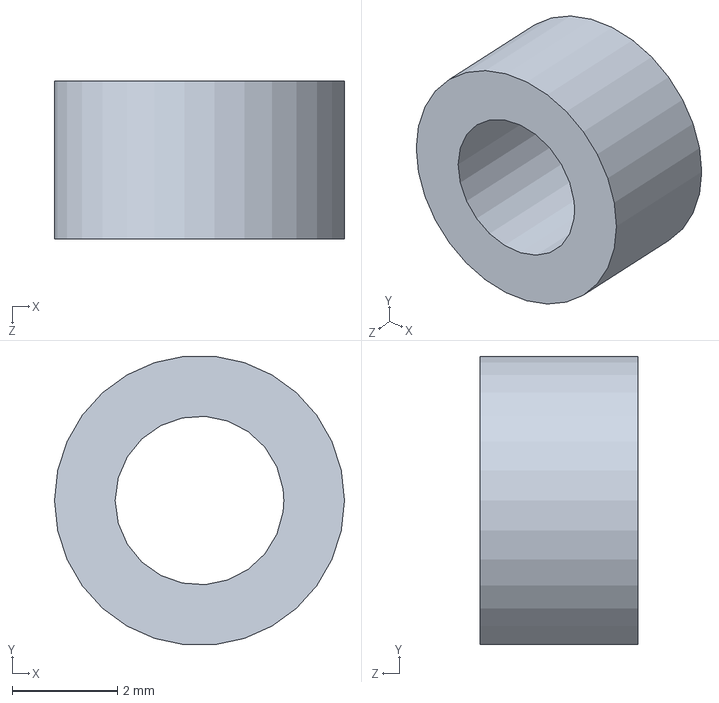
[picture p123: CAD file, 2022-07-06]
assets/fanatec-csp-v2-1.snapshot.5/47 - Entretoise capteur.SLDPRT
5.50 x 5.47 x 3.00 mm
