lazenyuk-dmitry/SterringWheel/assets/kfl-bearing-or-block-flange-ball-bearing-1.snapshot.10/Bearing KFL series/KFL007 block flange ball bearing 35 diameter shaft.SLDPRT

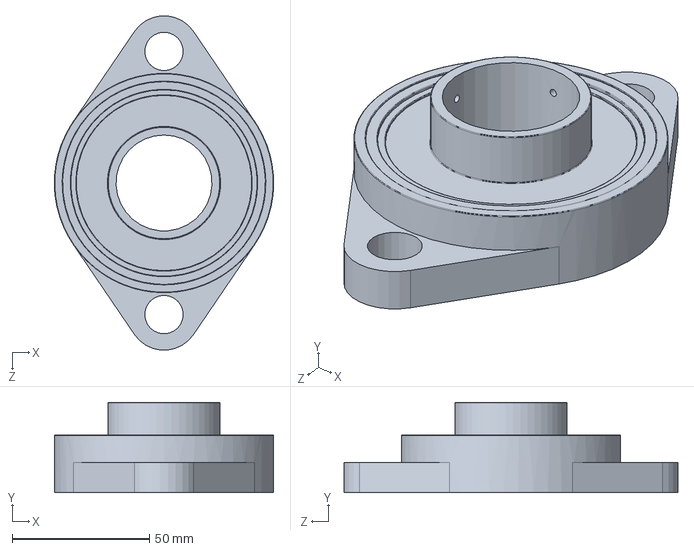
[picture p124: CAD file, 2022-05-09]
assets/kfl-bearing-or-block-flange-ball-bearing-1.snapshot.10/Bearing KFL series/KFL007 block flange ball bearing 35 diameter shaft.SLDPRT
80.0 x 33.0 x 121.8 mm
