lazenyuk-dmitry/SterringWheel/SterringWheel-Base.FCStd

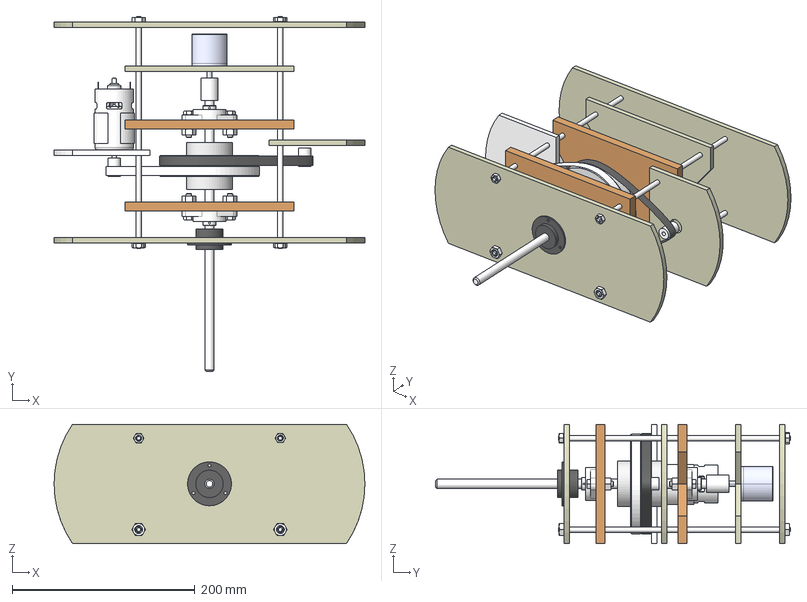
[picture p125: CAD file, 2022-05-12]
SterringWheel-Base.FCStd
340.0 x 388.3 x 130.3 mm
Передняя панель
Скользящий контакт
Крепление энкодера
Encoder hn3806
Передняя стойка подшипника
KFL000 block flange ball bearing 10mm diameter shaft
M6x25-Screw
M8-Nut
M6x25-Screw001
M8-Nut001
Задняя стойка подшипника
KFL000 block flange ball bearing 10mm diameter shaft001
M6x25-Screw003
M8-Nut003
M6x25-Screw002
M8-Nut002
Муфта вал-энкодер
M10x300.0-ThreadedRod
Редуктор 160T
Редуктор 160T001
Опора
T16
Ремень
Опора двигателя (mirrored)
Задняя панель
M6x254.0-ThreadedRod
M6x254.0-ThreadedRod001
M6x254.0-ThreadedRod002
M6x254.0-ThreadedRod003
M6-Nut001
M6-Nut
M6-Nut002
M8-Nut004
M8-Nut006
M8-Nut007
M8-Nut008
M8-Nut009
