lazenyuk-dmitry/SterringWheel/assets/bts7960-43a-high-power-h-bridge-module-1.snapshot.10/BTN7960 IC, BTS7960 43A HIGH POWER H BRIDGE MODULE.SLDPRT

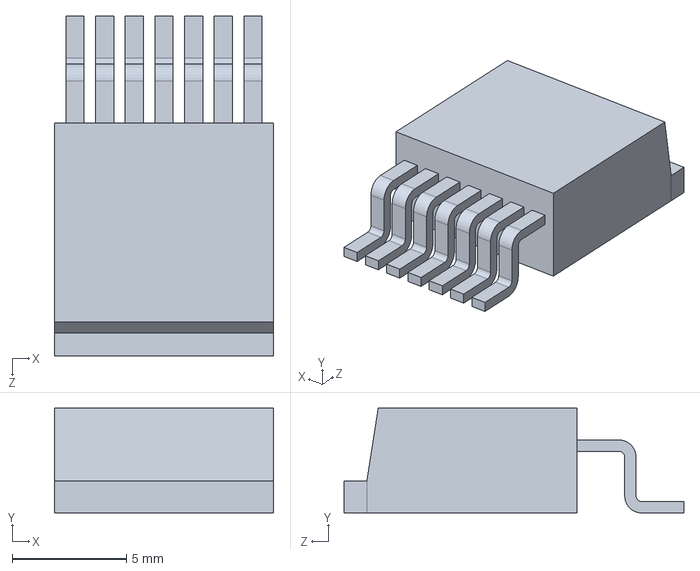
[picture p126: CAD file, 2022-05-12]
assets/bts7960-43a-high-power-h-bridge-module-1.snapshot.10/BTN7960 IC, BTS7960 43A HIGH POWER H BRIDGE MODULE.SLDPRT
9.60 x 4.60 x 14.9 mm
