lazenyuk-dmitry/SterringWheel/assets/fanatec-csp-v2-1.snapshot.5/22 - Biellette embrayage.SLDPRT

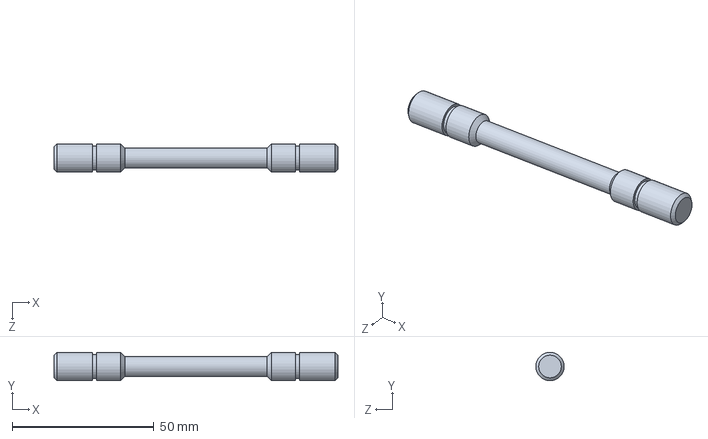
[picture p127: CAD file, 2022-07-06]
assets/fanatec-csp-v2-1.snapshot.5/22 - Biellette embrayage.SLDPRT
100.0 x 10.0 x 10.0 mm
