lazenyuk-dmitry/SterringWheel/assets/bts7960-43a-high-power-h-bridge-module-1.snapshot.10/NXP 74HC244D, BUFFER AND LINE DRIVER, BTS7960 43A HIGH POWER H BRIDGE MODULE.SLDPRT

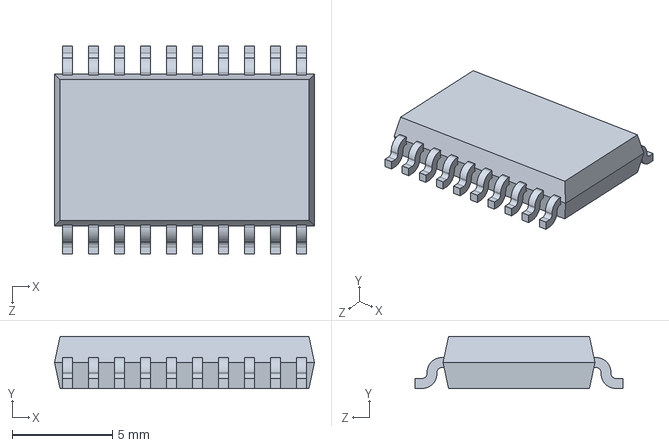
[picture p128: CAD file, 2022-05-12]
assets/bts7960-43a-high-power-h-bridge-module-1.snapshot.10/NXP 74HC244D, BUFFER AND LINE DRIVER, BTS7960 43A HIGH POWER H BRIDGE MODULE.SLDPRT
13.0 x 2.60 x 10.4 mm
