lazenyuk-dmitry/SterringWheel/assets/fanatec-csp-v2-1.snapshot.5/46 - Support controleur.SLDPRT

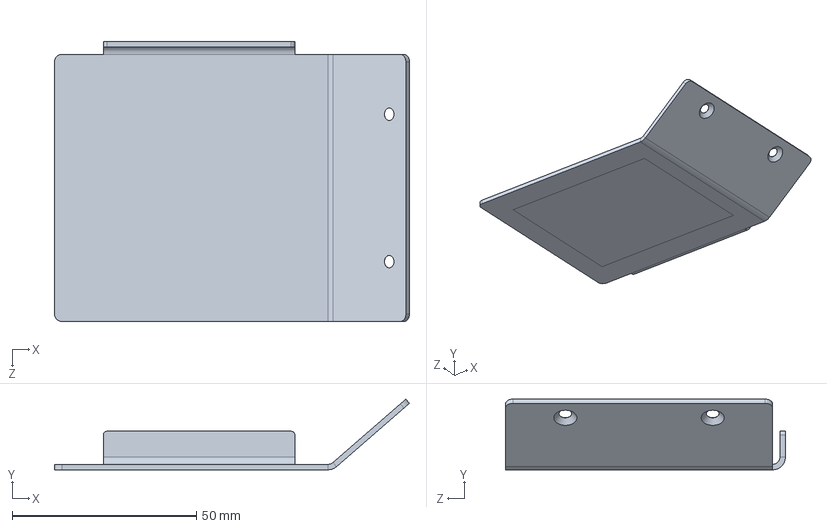
[picture p129: CAD file, 2022-07-06]
assets/fanatec-csp-v2-1.snapshot.5/46 - Support controleur.SLDPRT
96.4 x 19.2 x 76.0 mm
