lazenyuk-dmitry/SterringWheel/assets/kfl-bearing-or-block-flange-ball-bearing-1.snapshot.10/step files/KFL004 block flange ball bearing 20 diameter shaft.STEP

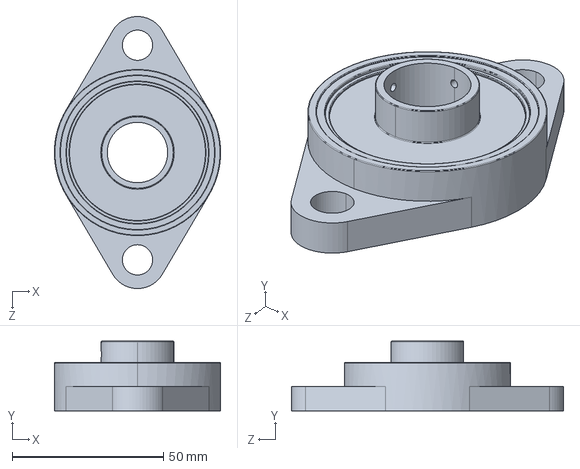
[picture p130: CAD file, 2022-05-09]
assets/kfl-bearing-or-block-flange-ball-bearing-1.snapshot.10/step files/KFL004 block flange ball bearing 20 diameter shaft.STEP
55.0 x 23.0 x 90.0 mm
