lazenyuk-dmitry/SterringWheel/assets/bts7960-43a-high-power-h-bridge-module-1.snapshot.10/HEATSINK, BTS7960 43A HIGH POWER H BRIDGE MODULE.SLDPRT

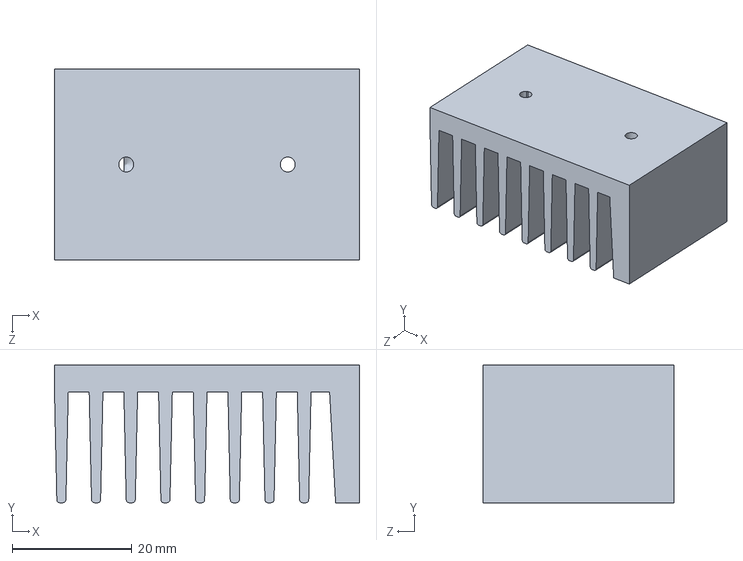
[picture p131: CAD file, 2022-05-12]
assets/bts7960-43a-high-power-h-bridge-module-1.snapshot.10/HEATSINK, BTS7960 43A HIGH POWER H BRIDGE MODULE.SLDPRT
51.0 x 23.0 x 32.0 mm
