lazenyuk-dmitry/SterringWheel/assets/fanatec-csp-v2-1.snapshot.5/19 - Axe capteur.SLDPRT

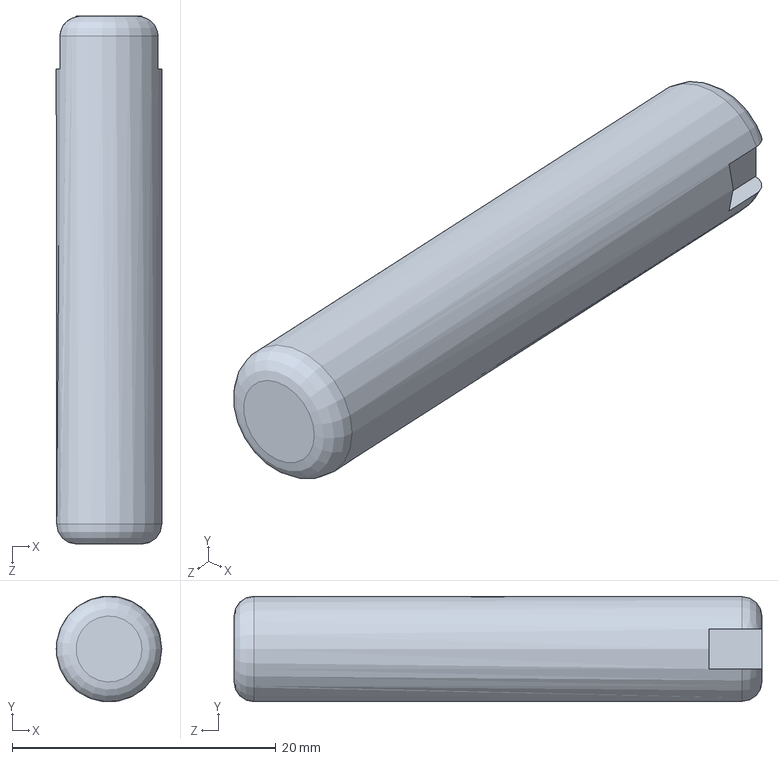
[picture p132: CAD file, 2022-07-06]
assets/fanatec-csp-v2-1.snapshot.5/19 - Axe capteur.SLDPRT
8.00 x 7.98 x 40.0 mm
