lazenyuk-dmitry/SterringWheel/assets/fanatec-csp-v2-1.snapshot.5/10 - Levier pedales F.SLDPRT

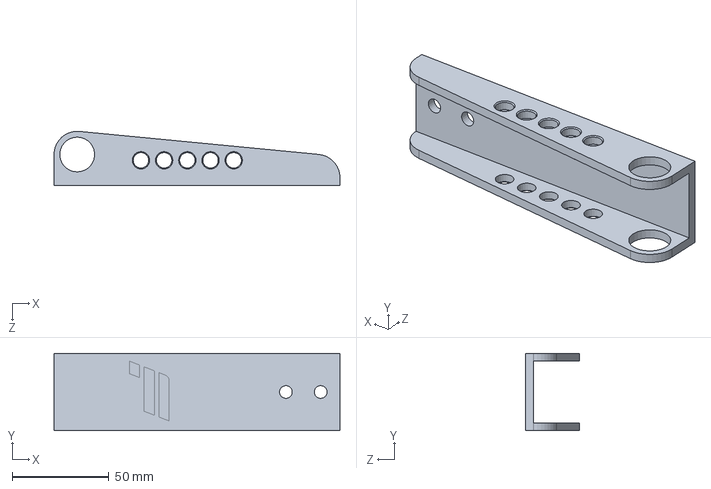
[picture p133: CAD file, 2022-07-06]
assets/fanatec-csp-v2-1.snapshot.5/10 - Levier pedales F.SLDPRT
148.0 x 40.0 x 28.1 mm
