lazenyuk-dmitry/SterringWheel/assets/kfl-bearing-or-block-flange-ball-bearing-1.snapshot.10/step files/KFL002 block flange ball bearing 15 diameter shaft.STEP

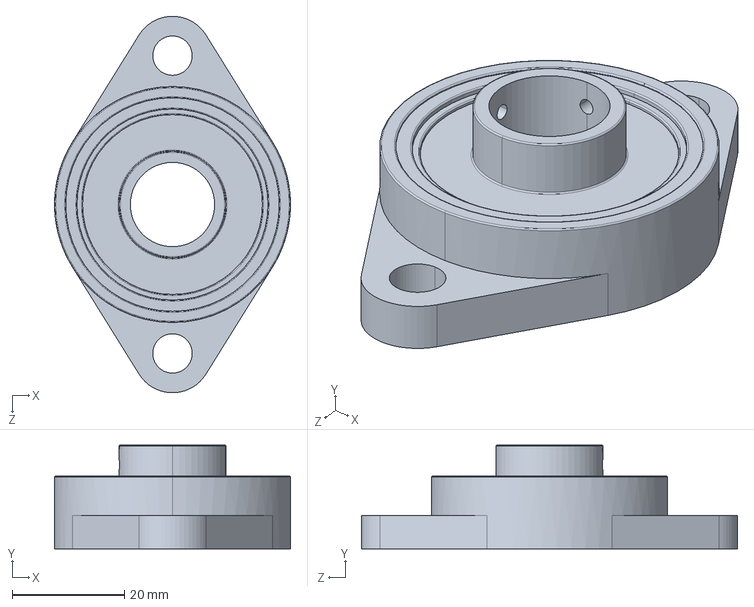
[picture p134: CAD file, 2022-05-09]
assets/kfl-bearing-or-block-flange-ball-bearing-1.snapshot.10/step files/KFL002 block flange ball bearing 15 diameter shaft.STEP
42.0 x 18.5 x 67.0 mm
