lazenyuk-dmitry/SterringWheel/assets/fanatec-csp-v2-1.snapshot.5/33 - Entretoise pedale.SLDPRT

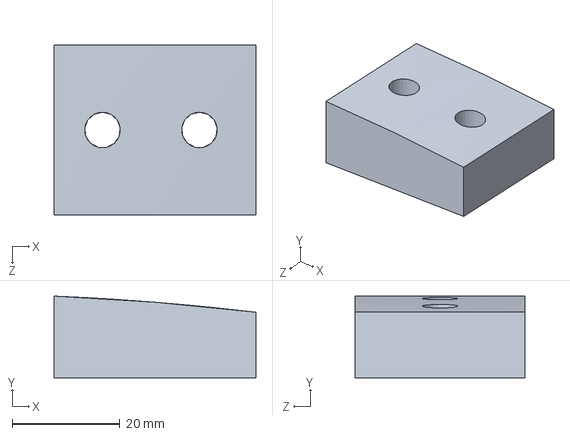
[picture p135: CAD file, 2022-07-06]
assets/fanatec-csp-v2-1.snapshot.5/33 - Entretoise pedale.SLDPRT
37.5 x 15.2 x 31.5 mm
