lazenyuk-dmitry/SterringWheel/assets/fanatec-csp-v2-1.snapshot.5/04 - Equerre fixation sol SYM.SLDPRT

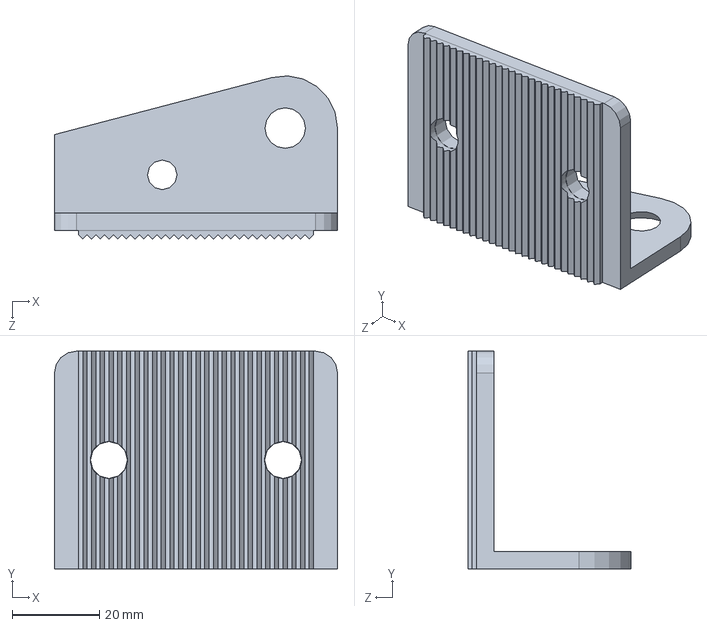
[picture p136: CAD file, 2022-07-06]
assets/fanatec-csp-v2-1.snapshot.5/04 - Equerre fixation sol SYM.SLDPRT
65.0 x 50.0 x 37.5 mm
