lazenyuk-dmitry/SterringWheel/assets/fanatec-csp-v2-1.snapshot.5/43 - Barre transversale.SLDPRT

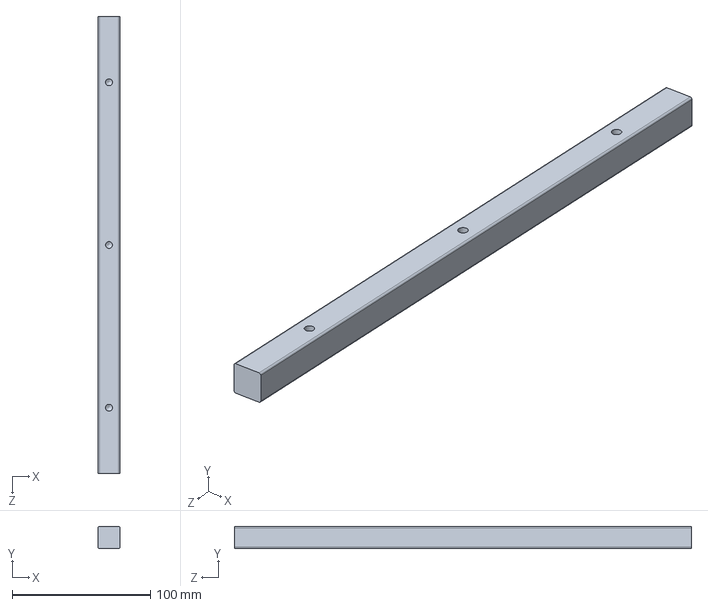
[picture p137: CAD file, 2022-07-06]
assets/fanatec-csp-v2-1.snapshot.5/43 - Barre transversale.SLDPRT
16.0 x 16.0 x 330.0 mm
