lazenyuk-dmitry/SterringWheel/assets/fanatec-csp-v2-1.snapshot.5/08 - Axe long.SLDPRT

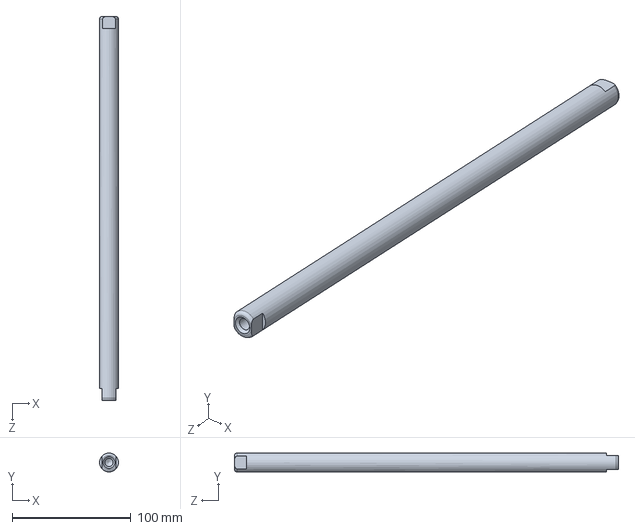
[picture p138: CAD file, 2022-07-06]
assets/fanatec-csp-v2-1.snapshot.5/08 - Axe long.SLDPRT
16.0 x 16.0 x 324.0 mm
