lazenyuk-dmitry/SterringWheel/assets/fanatec-csp-v2-1.snapshot.5/21 - Ressort embrayage.SLDPRT

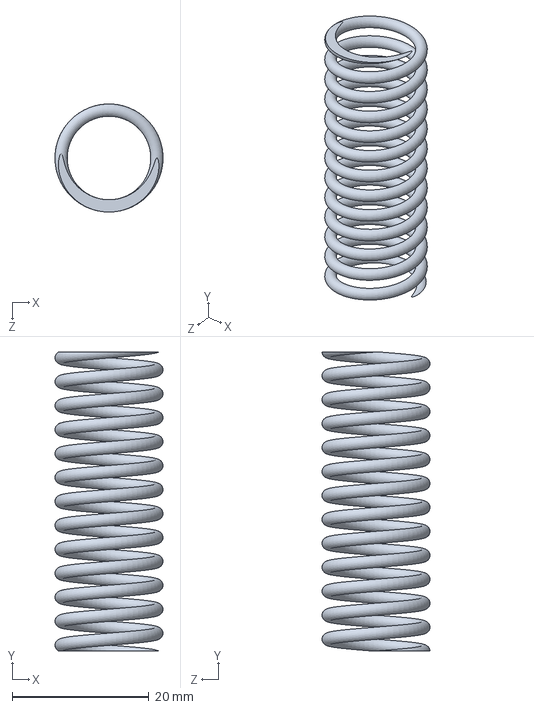
[picture p139: CAD file, 2022-07-06]
assets/fanatec-csp-v2-1.snapshot.5/21 - Ressort embrayage.SLDPRT
15.8 x 43.7 x 15.8 mm
