lazenyuk-dmitry/SterringWheel/assets/fanatec-csp-v2-1.snapshot.5/09 - Levier pedales A-E.SLDPRT

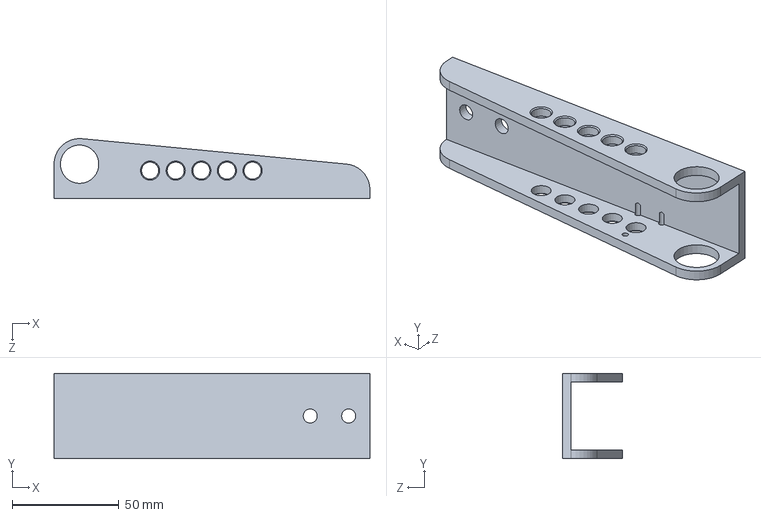
[picture p140: CAD file, 2022-07-06]
assets/fanatec-csp-v2-1.snapshot.5/09 - Levier pedales A-E.SLDPRT
148.0 x 40.0 x 28.0 mm
