lazenyuk-dmitry/SterringWheel/assets/fanatec-csp-v2-1.snapshot.5/16 - Coulisseau frein.SLDPRT

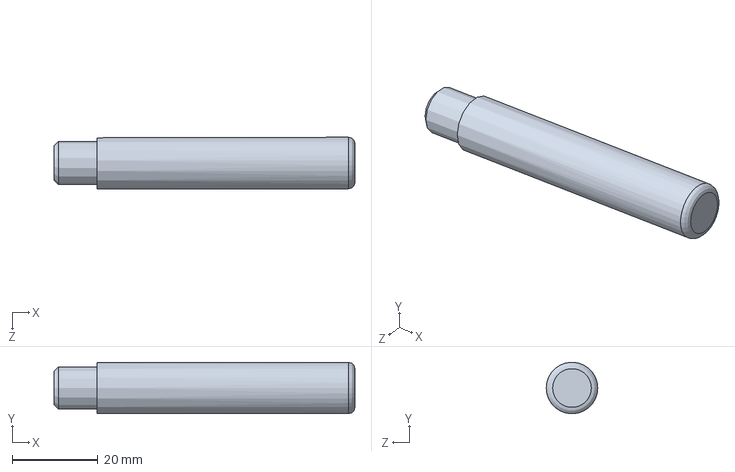
[picture p141: CAD file, 2022-07-06]
assets/fanatec-csp-v2-1.snapshot.5/16 - Coulisseau frein.SLDPRT
70.0 x 11.9 x 12.0 mm
