lazenyuk-dmitry/SterringWheel/assets/fanatec-csp-v2-1.snapshot.5/32 - Guide coulisseau frein.SLDPRT

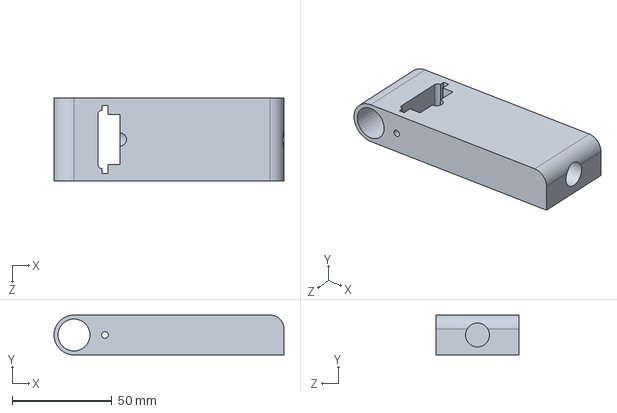
[picture p142: CAD file, 2022-07-06]
assets/fanatec-csp-v2-1.snapshot.5/32 - Guide coulisseau frein.SLDPRT
115.0 x 20.0 x 41.6 mm
