lazenyuk-dmitry/SterringWheel/assets/fanatec-csp-v2-1.snapshot.5/37 - Repose pied.SLDPRT

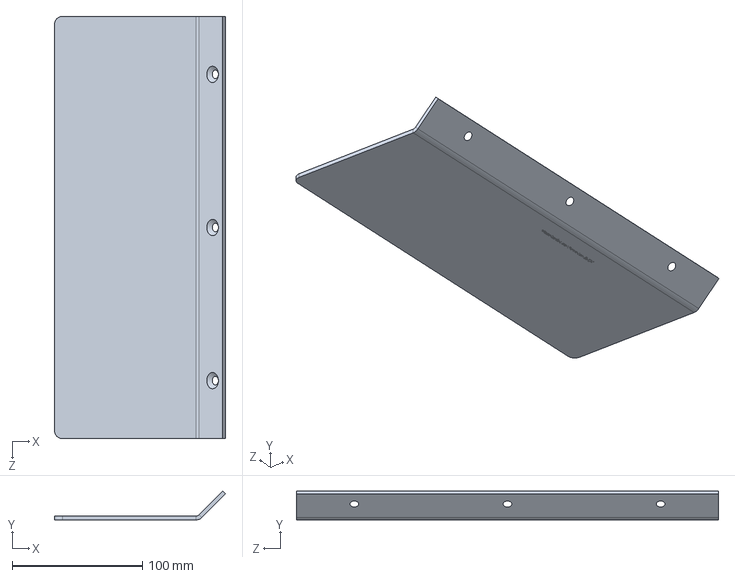
[picture p143: CAD file, 2022-07-06]
assets/fanatec-csp-v2-1.snapshot.5/37 - Repose pied.SLDPRT
131.2 x 22.1 x 324.0 mm
