lazenyuk-dmitry/SterringWheel/assets/fanatec-csp-v2-1.snapshot.5/42 - Ressort frein.SLDPRT

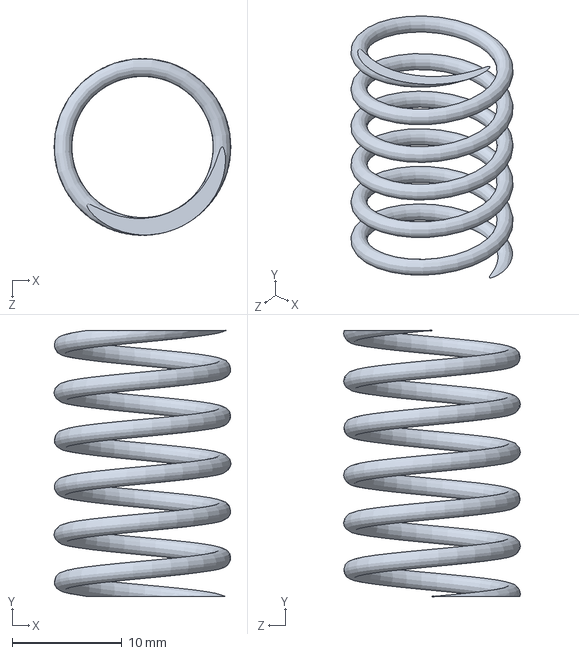
[picture p144: CAD file, 2022-07-06]
assets/fanatec-csp-v2-1.snapshot.5/42 - Ressort frein.SLDPRT
16.1 x 24.2 x 16.1 mm
