lazenyuk-dmitry/SterringWheel/assets/fanatec-csp-v2-1.snapshot.5/20 - Coulisseau embrayage.SLDPRT

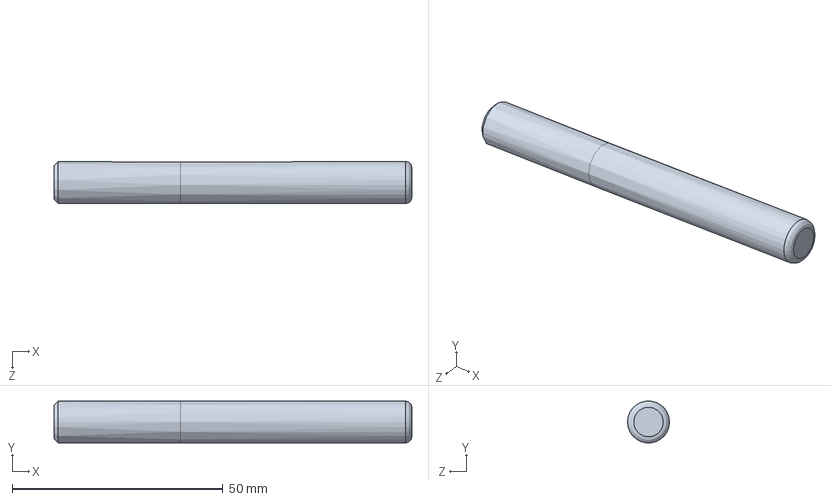
[picture p145: CAD file, 2022-07-06]
assets/fanatec-csp-v2-1.snapshot.5/20 - Coulisseau embrayage.SLDPRT
85.0 x 9.93 x 10.0 mm
