lazenyuk-dmitry/SterringWheel/assets/fanatec-csp-v2-1.snapshot.5/01 - Pied.SLDPRT

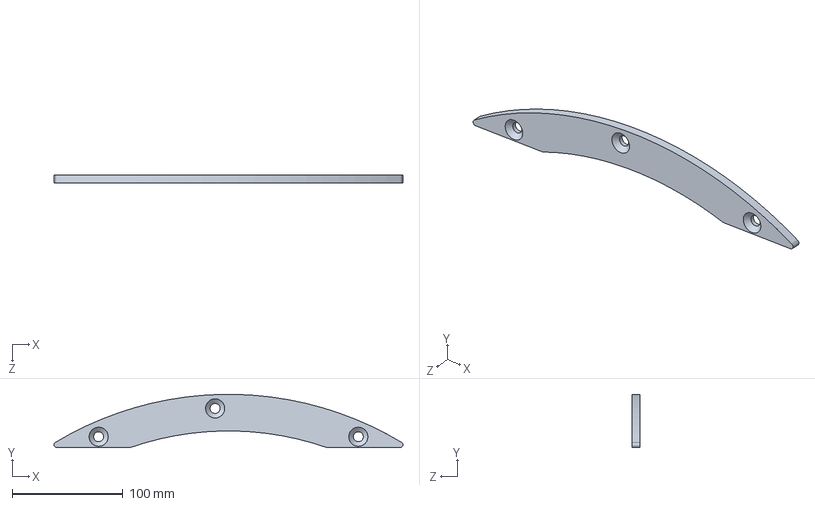
[picture p146: CAD file, 2022-07-06]
assets/fanatec-csp-v2-1.snapshot.5/01 - Pied.SLDPRT
314.5 x 47.9 x 7.50 mm
