lazenyuk-dmitry/SterringWheel/assets/fanatec-csp-v2-1.snapshot.5/34 - Patte suspension.SLDPRT

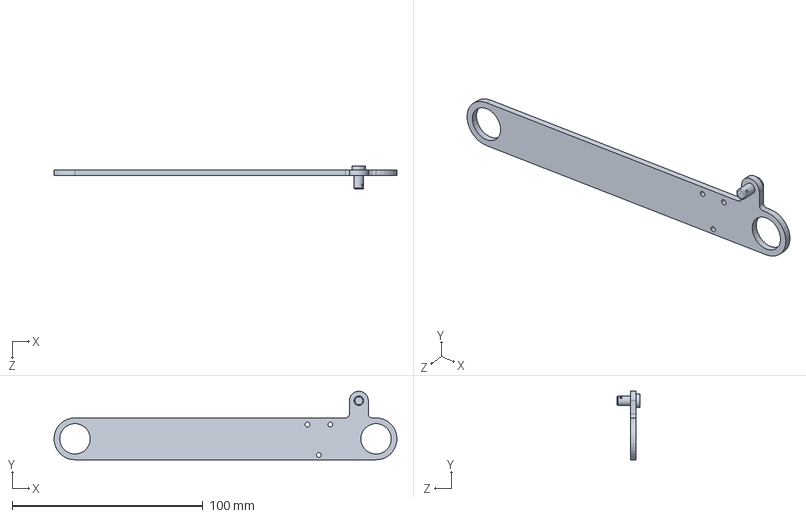
[picture p147: CAD file, 2022-07-06]
assets/fanatec-csp-v2-1.snapshot.5/34 - Patte suspension.SLDPRT
180.0 x 36.0 x 12.0 mm
