lazenyuk-dmitry/SterringWheel/assets/fanatec-csp-v2-1.snapshot.5/17 - Axe nu.SLDPRT

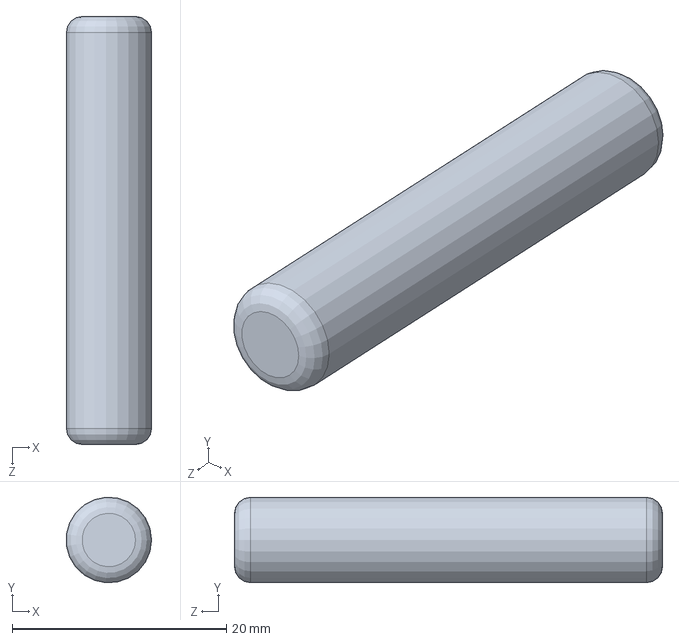
[picture p148: CAD file, 2022-07-06]
assets/fanatec-csp-v2-1.snapshot.5/17 - Axe nu.SLDPRT
7.96 x 7.98 x 40.0 mm
