lazenyuk-dmitry/SterringWheel/assets/fanatec-csp-v2-1.snapshot.5/41 - Ressort accelerateur.SLDPRT

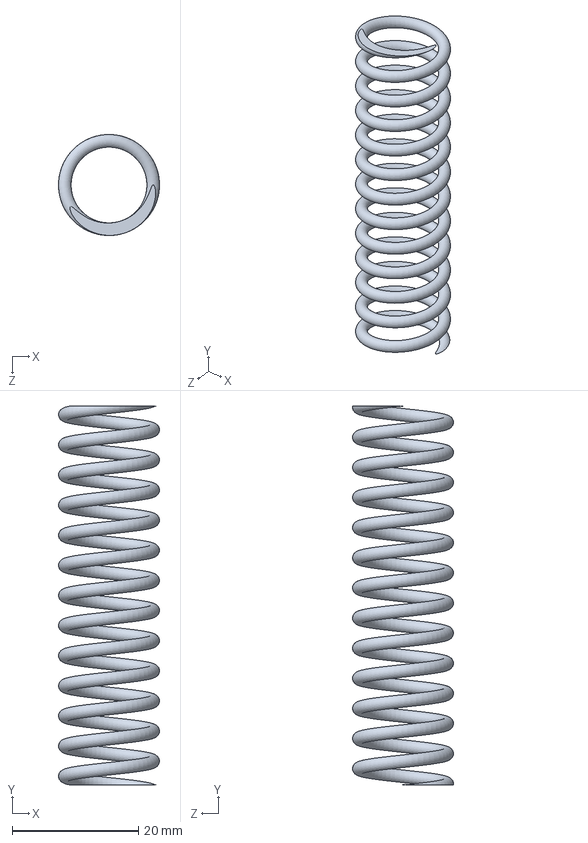
[picture p149: CAD file, 2022-07-06]
assets/fanatec-csp-v2-1.snapshot.5/41 - Ressort accelerateur.SLDPRT
16.0 x 60.0 x 16.0 mm
