lazenyuk-dmitry/SterringWheel/assets/fanatec-csp-v2-1.snapshot.5/02 - Pied SYM.SLDPRT

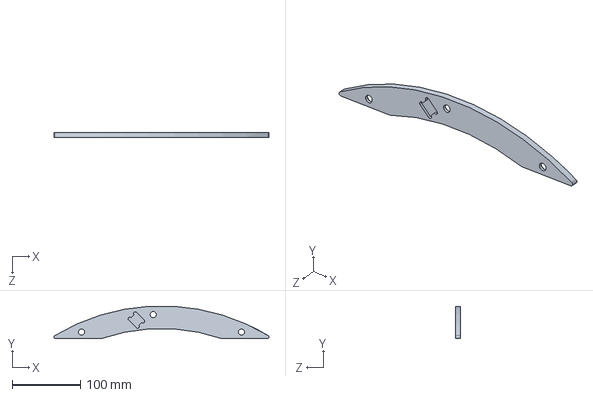
[picture p150: CAD file, 2022-07-06]
assets/fanatec-csp-v2-1.snapshot.5/02 - Pied SYM.SLDPRT
314.5 x 47.5 x 7.50 mm
