lazenyuk-dmitry/SterringWheel/assets/fanatec-csp-v2-1.snapshot.5/29 - Entretoise.SLDPRT

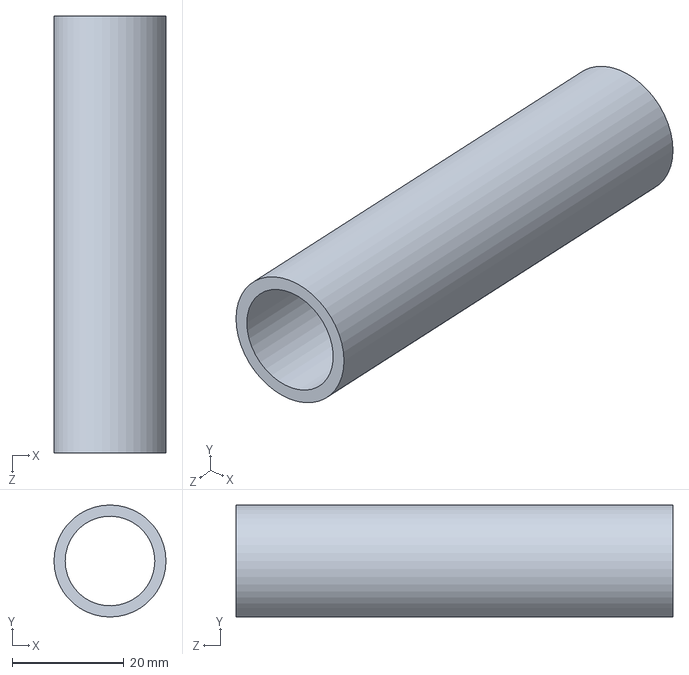
[picture p151: CAD file, 2022-07-06]
assets/fanatec-csp-v2-1.snapshot.5/29 - Entretoise.SLDPRT
20.0 x 20.0 x 78.0 mm
