lazenyuk-dmitry/SterringWheel/assets/fanatec-csp-v2-1.snapshot.5/49 - Potentiometre.SLDPRT

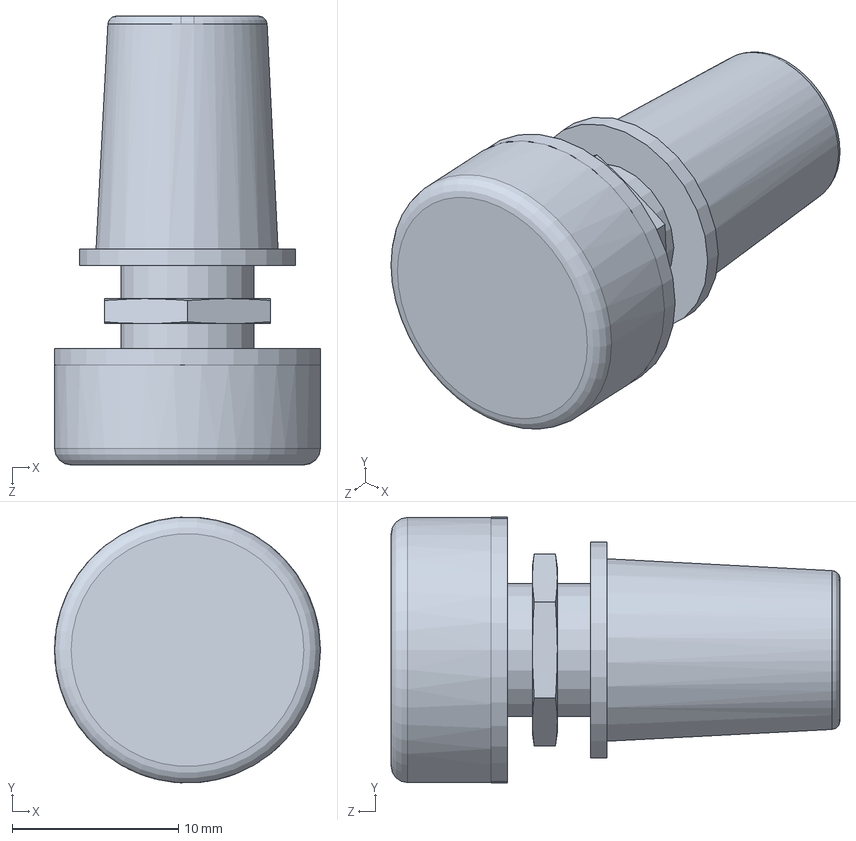
[picture p152: CAD file, 2022-07-06]
assets/fanatec-csp-v2-1.snapshot.5/49 - Potentiometre.SLDPRT
16.0 x 16.0 x 27.0 mm
