lazenyuk-dmitry/SterringWheel/assets/fanatec-csp-v2-1.snapshot.5/23 - Guide coulisseau simple.SLDPRT

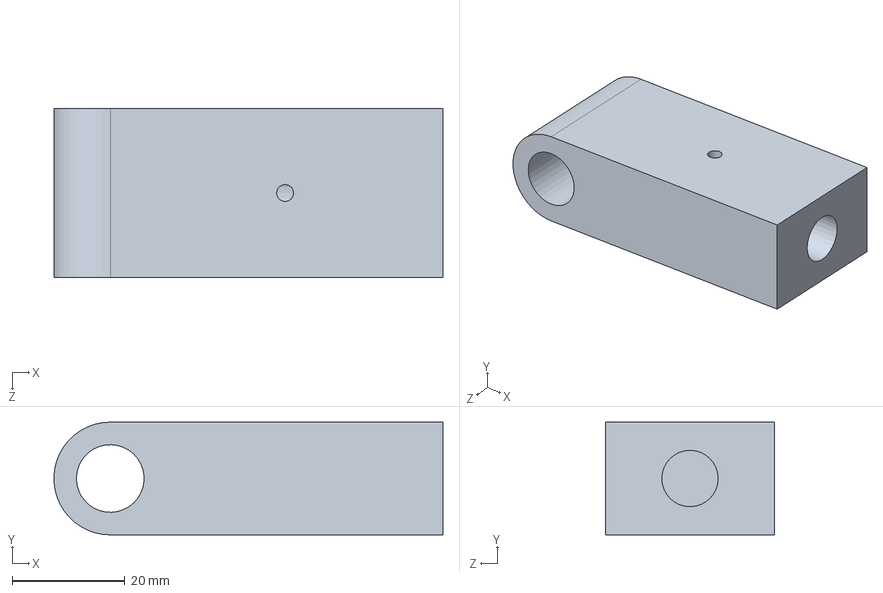
[picture p153: CAD file, 2022-07-06]
assets/fanatec-csp-v2-1.snapshot.5/23 - Guide coulisseau simple.SLDPRT
69.0 x 20.0 x 30.0 mm
