lazenyuk-dmitry/SterringWheel/assets/fanatec-csp-v2-1.snapshot.5/30 - Pousseur mousse.SLDPRT

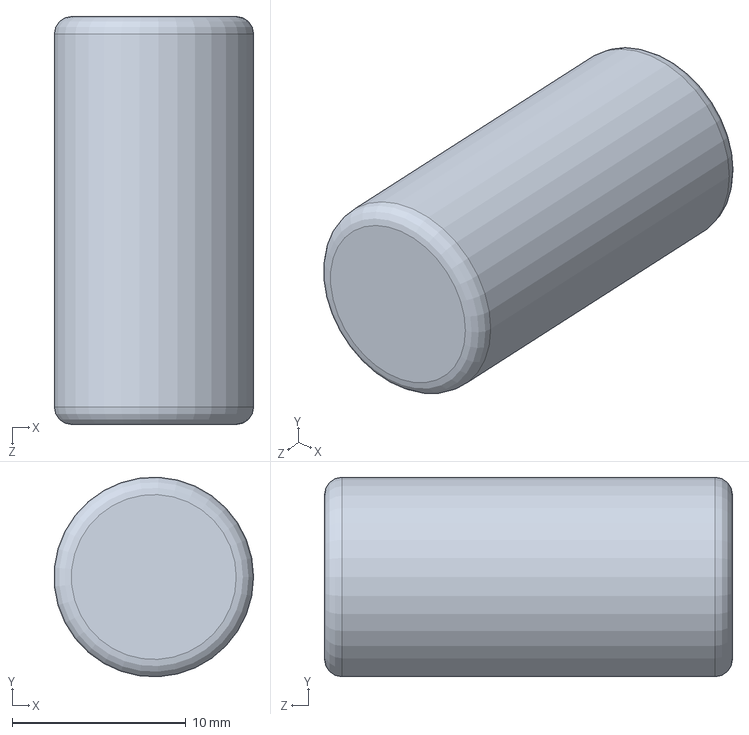
[picture p154: CAD file, 2022-07-06]
assets/fanatec-csp-v2-1.snapshot.5/30 - Pousseur mousse.SLDPRT
11.5 x 11.5 x 23.5 mm
