lazenyuk-dmitry/SterringWheel/assets/fanatec-csp-v2-1.snapshot.5/45 - Goupille.SLDPRT

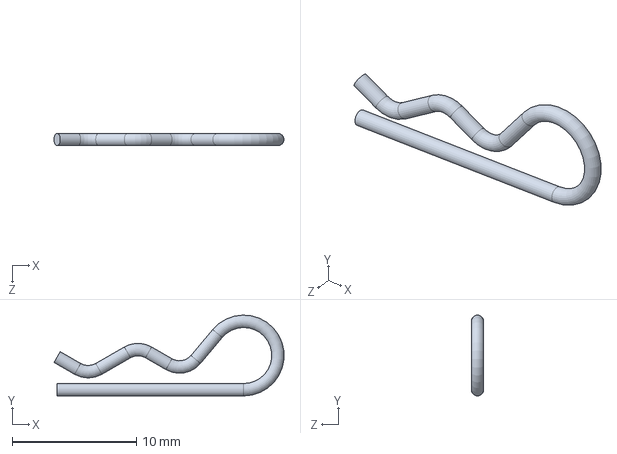
[picture p155: CAD file, 2022-07-06]
assets/fanatec-csp-v2-1.snapshot.5/45 - Goupille.SLDPRT
18.5 x 6.50 x 1.00 mm
