lazenyuk-dmitry/SterringWheel/assets/fanatec-csp-v2-1.snapshot.5/27 - Axe 8mm.SLDPRT

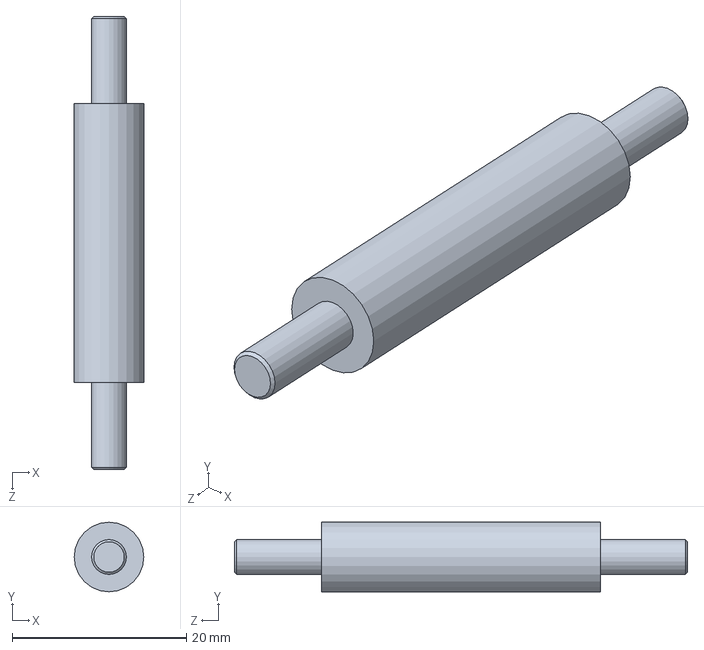
[picture p156: CAD file, 2022-07-06]
assets/fanatec-csp-v2-1.snapshot.5/27 - Axe 8mm.SLDPRT
8.00 x 8.00 x 52.0 mm
