lazenyuk-dmitry/SterringWheel/assets/fanatec-csp-v2-1.snapshot.5/15 - Pivot levier.SLDPRT

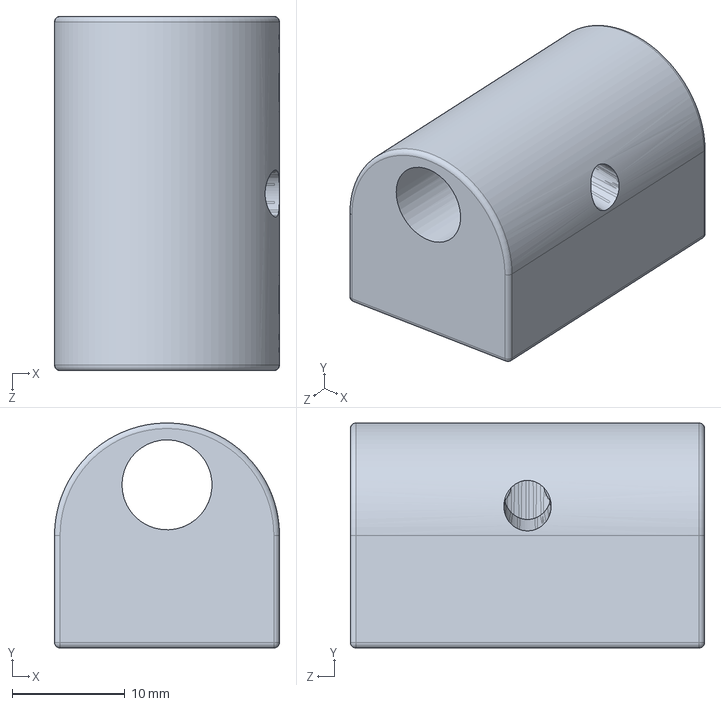
[picture p157: CAD file, 2022-07-06]
assets/fanatec-csp-v2-1.snapshot.5/15 - Pivot levier.SLDPRT
20.0 x 20.0 x 31.5 mm
