lazenyuk-dmitry/SterringWheel/assets/fanatec-csp-v2-1.snapshot.5/25 - Tampon embrayage.SLDPRT

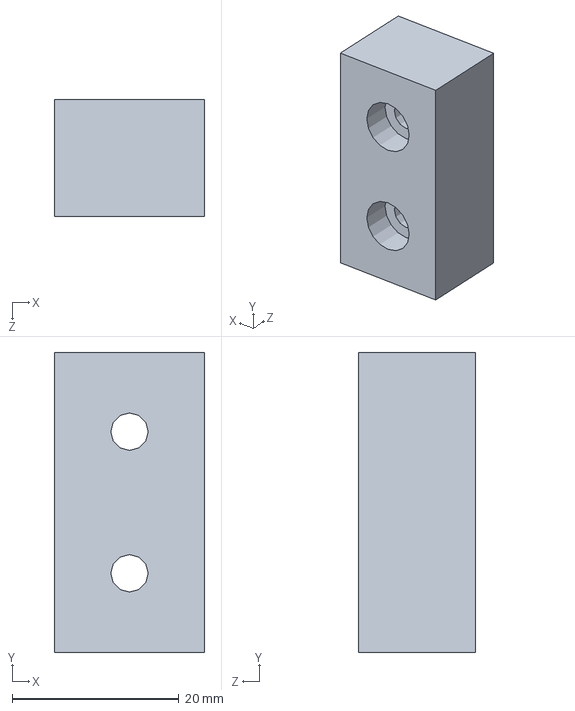
[picture p159: CAD file, 2022-07-06]
assets/fanatec-csp-v2-1.snapshot.5/25 - Tampon embrayage.SLDPRT
18.0 x 36.0 x 14.0 mm
