lazenyuk-dmitry/SterringWheel/assets/fanatec-csp-v2-1.snapshot.5/31 - Mousse loadcell.SLDPRT

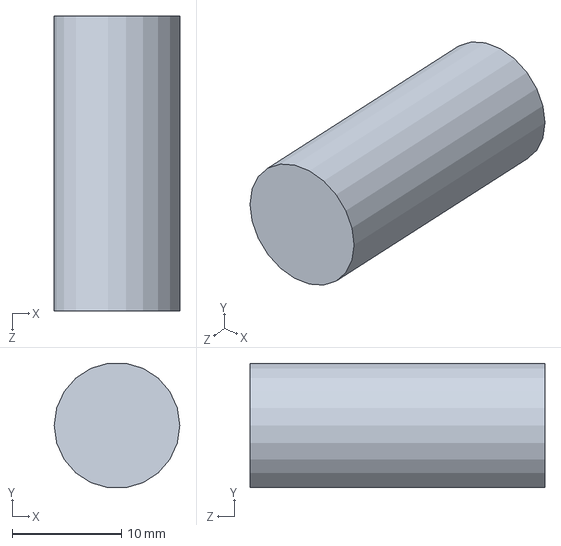
[picture p161: CAD file, 2022-07-06]
assets/fanatec-csp-v2-1.snapshot.5/31 - Mousse loadcell.SLDPRT
11.5 x 11.4 x 27.0 mm
