lazenyuk-dmitry/SterringWheel/assets/fanatec-csp-v2-1.snapshot.5/44 - Pedale A.SLDPRT

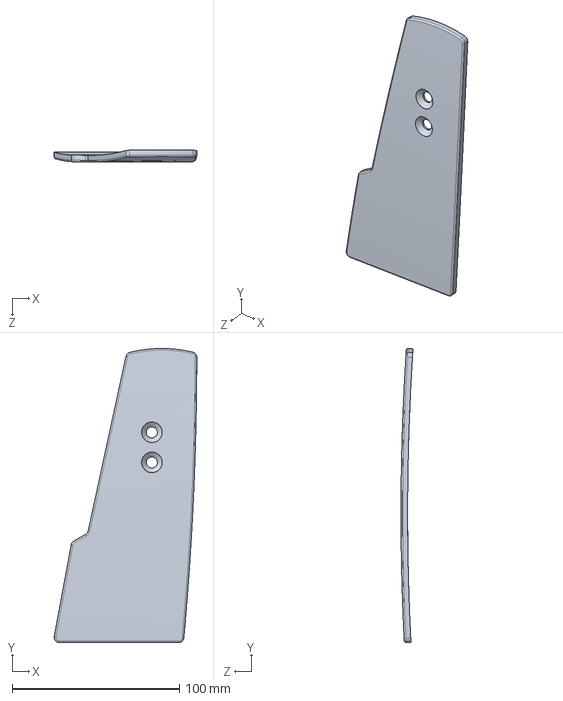
[picture p162: CAD file, 2022-07-06]
assets/fanatec-csp-v2-1.snapshot.5/44 - Pedale A.SLDPRT
85.4 x 176.0 x 7.23 mm
