lazenyuk-dmitry/SterringWheel/assets/fanatec-csp-v2-1.snapshot.5/28 - Pivot renvoi.SLDPRT

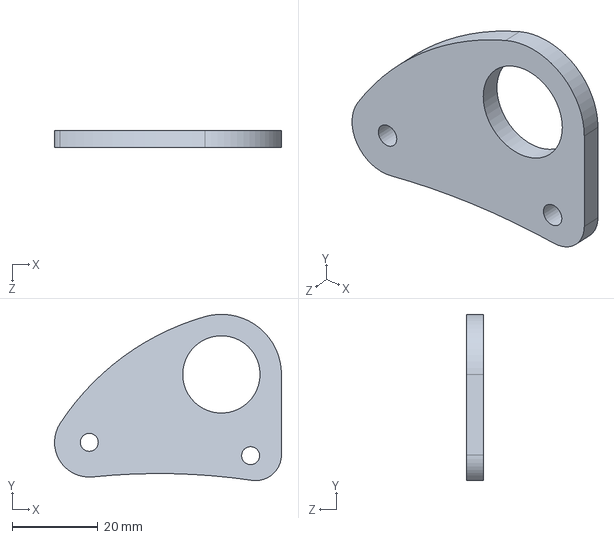
[picture p163: CAD file, 2022-07-06]
assets/fanatec-csp-v2-1.snapshot.5/28 - Pivot renvoi.SLDPRT
52.9 x 38.7 x 4.00 mm
