lazenyuk-dmitry/SterringWheel/assets/fanatec-csp-v2-1.snapshot.5/13 - Ecrou suspension.SLDPRT

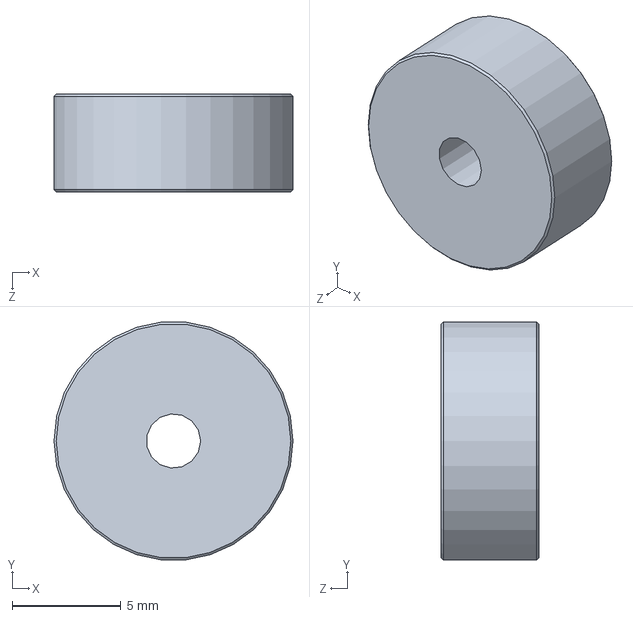
[picture p164: CAD file, 2022-07-06]
assets/fanatec-csp-v2-1.snapshot.5/13 - Ecrou suspension.SLDPRT
11.0 x 10.9 x 4.50 mm
