lazenyuk-dmitry/SterringWheel/assets/fanatec-csp-v2-1.snapshot.5/26 - Axe 12mm.SLDPRT

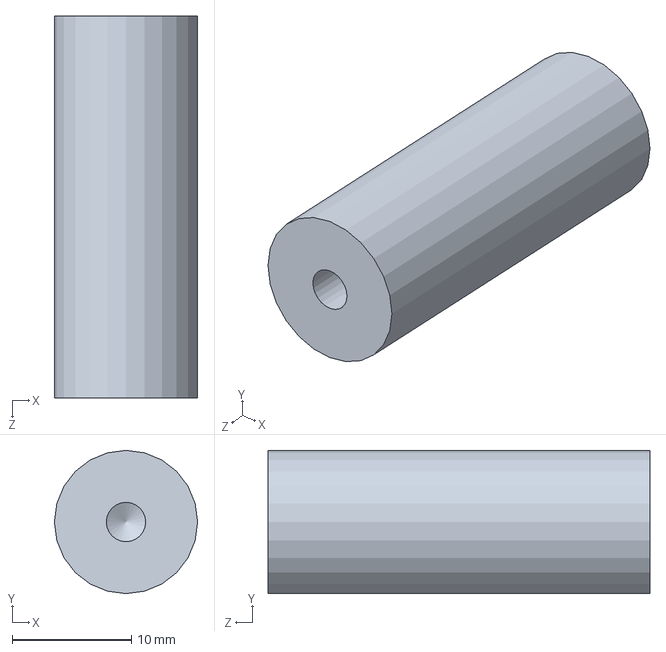
[picture p165: CAD file, 2022-07-06]
assets/fanatec-csp-v2-1.snapshot.5/26 - Axe 12mm.SLDPRT
12.0 x 12.0 x 32.0 mm
