lazenyuk-dmitry/SterringWheel/assets/fanatec-csp-v2-1.snapshot.5/36 - Loadcell.SLDPRT

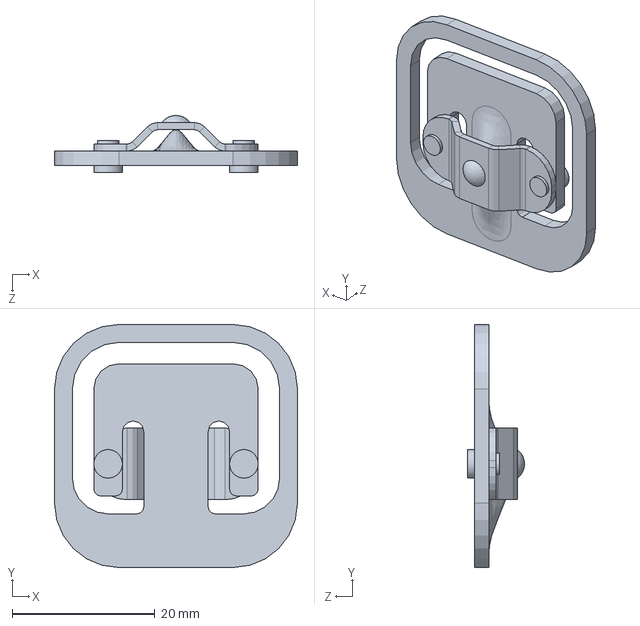
[picture p166: CAD file, 2022-07-06]
assets/fanatec-csp-v2-1.snapshot.5/36 - Loadcell.SLDPRT
34.0 x 34.0 x 8.00 mm
