lazenyuk-dmitry/SterringWheel/assets/fanatec-csp-v2-1.snapshot.5/12 - Pivot suspension.SLDPRT

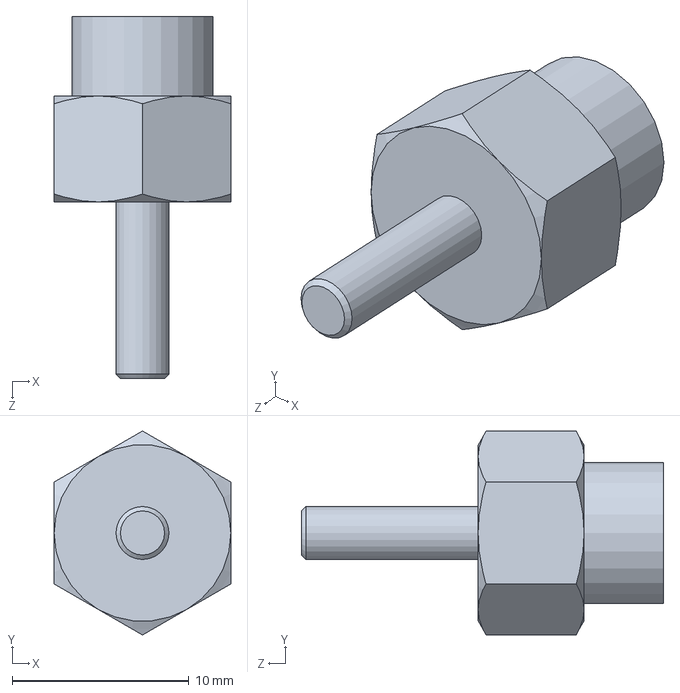
[picture p167: CAD file, 2022-07-06]
assets/fanatec-csp-v2-1.snapshot.5/12 - Pivot suspension.SLDPRT
10.0 x 11.5 x 20.5 mm
