lazenyuk-dmitry/SterringWheel/assets/fanatec-csp-v2-1.snapshot.5/48 - Capteur hall.SLDPRT

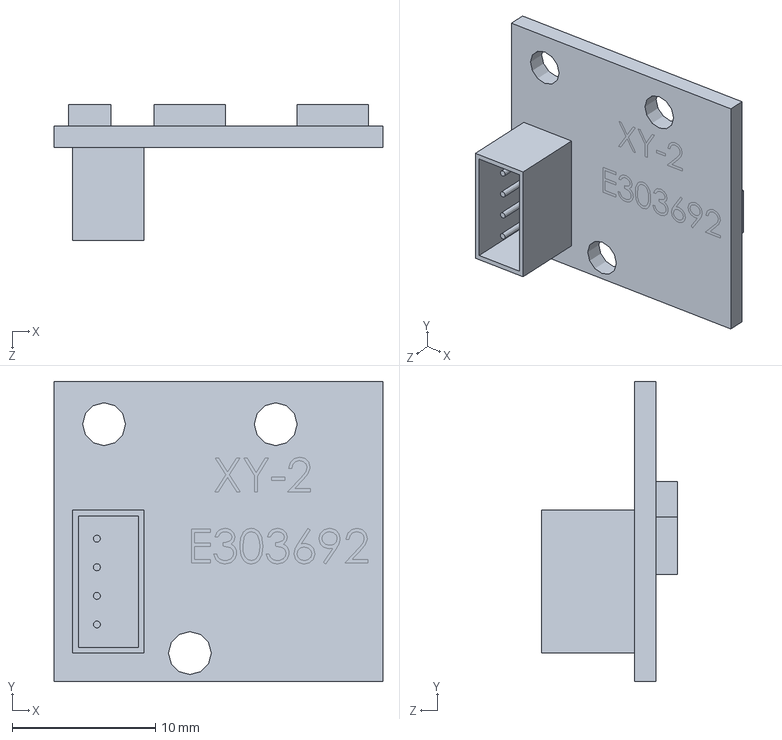
[picture p169: CAD file, 2022-07-06]
assets/fanatec-csp-v2-1.snapshot.5/48 - Capteur hall.SLDPRT
23.0 x 21.0 x 9.50 mm
