lazenyuk-dmitry/SterringWheel/assets/fanatec-csp-v2-1.snapshot.5/35 - Patte potentiometre.SLDPRT

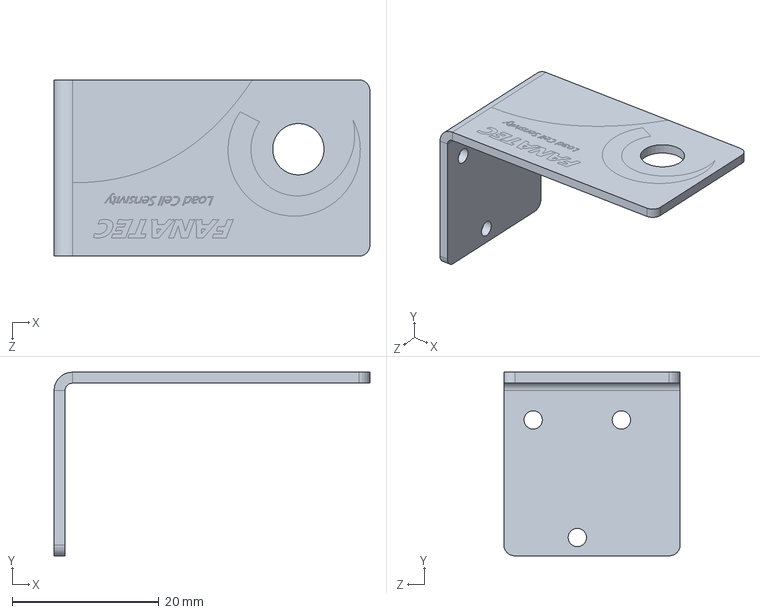
[picture p170: CAD file, 2022-07-06]
assets/fanatec-csp-v2-1.snapshot.5/35 - Patte potentiometre.SLDPRT
43.0 x 25.0 x 24.0 mm
