lazenyuk-dmitry/SterringWheel/assets/fanatec-csp-v2-1.snapshot.5/14 - Amortisseur.SLDPRT

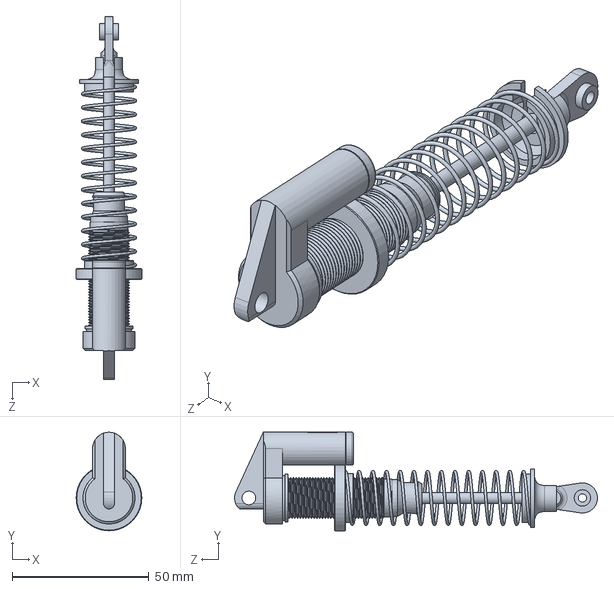
[picture p171: CAD file, 2022-07-06]
assets/fanatec-csp-v2-1.snapshot.5/14 - Amortisseur.SLDPRT
24.0 x 36.0 x 132.5 mm
