lazenyuk-dmitry/SterringWheel/assets/6-speed-lower-plate-for-noctiluxx-s-h-shifter-1.snapshot.2/IMG_20201108_220551.jpg

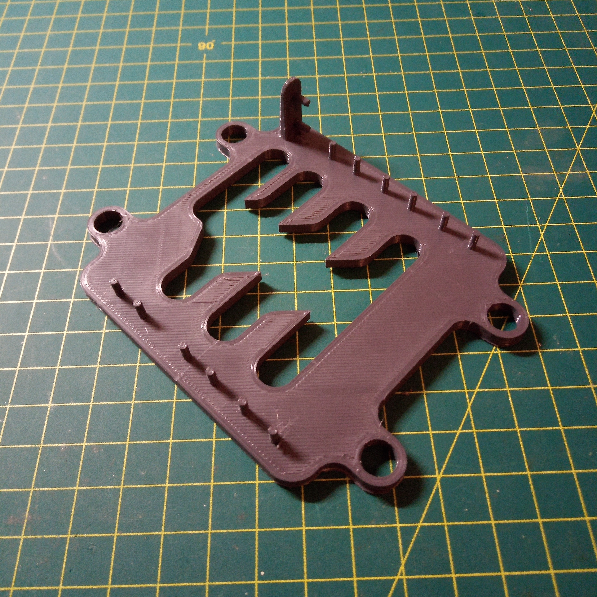
assets/6-speed-lower-plate-for-noctiluxx-s-h-shifter-1.snapshot.2/IMG_20201108_220551.jpg
